Zipra1/SlimeNRF-Fuimini/Dock/Dock PCB/silkscreen.png

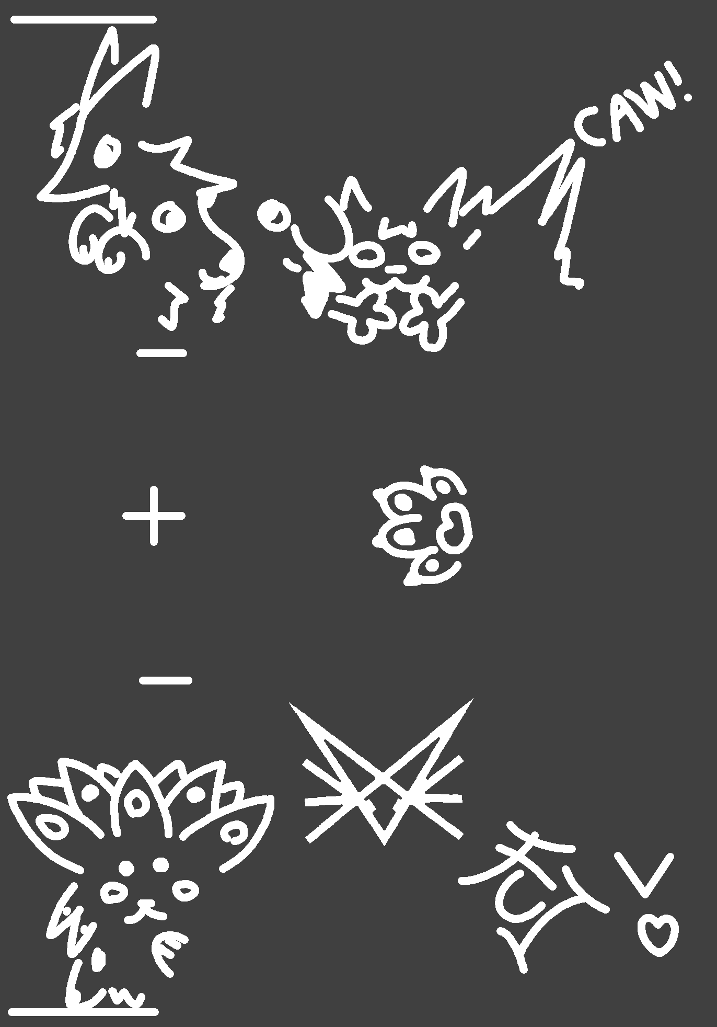
Dock/Dock PCB/silkscreen.png
