Zipra1/SlimeNRF-Fuimini/Dock/Photos/Processed/backhang.png

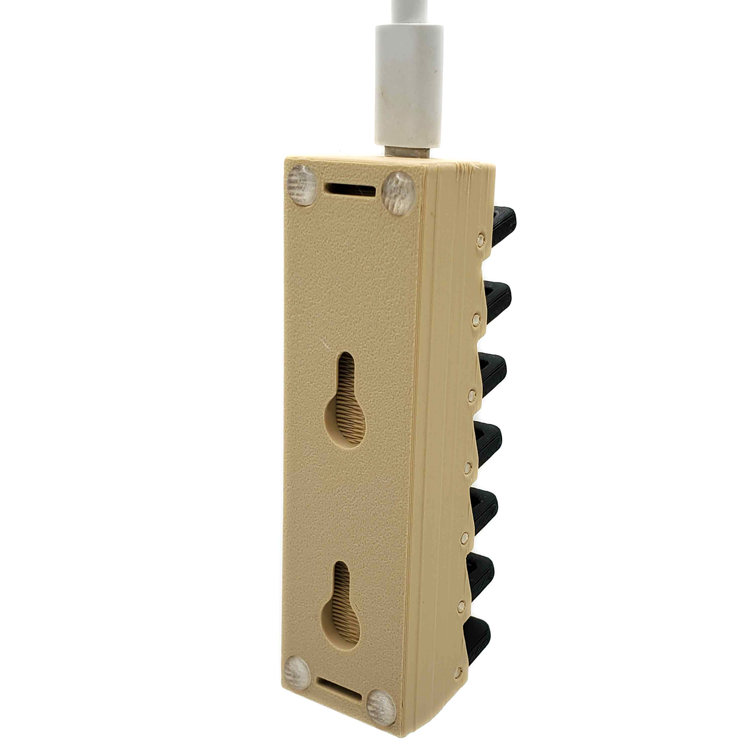
Dock/Photos/Processed/backhang.png
