Zipra1/SlimeNRF-Fuimini/Dock/Photos/Processed/fronthang.png

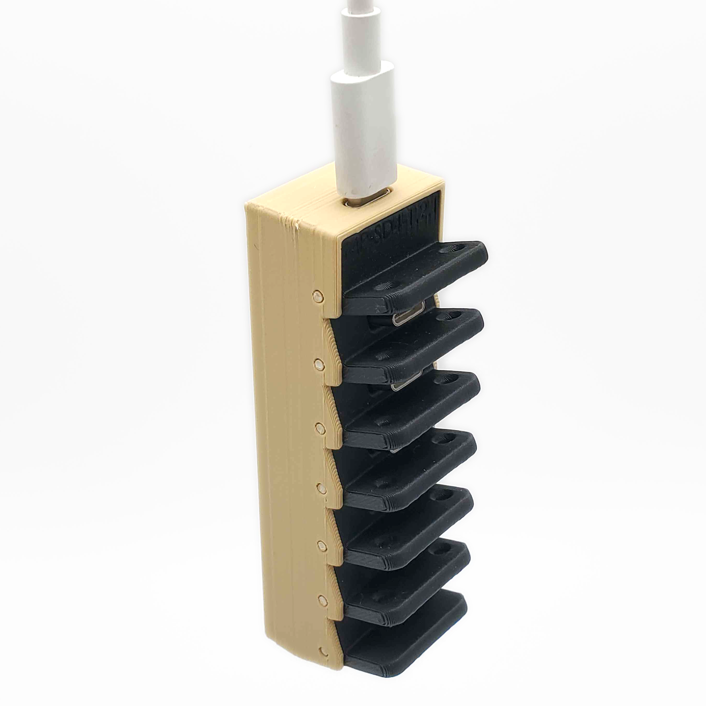
Dock/Photos/Processed/fronthang.png
