Zipra1/SlimeNRF-Fuimini/Dock/Photos/Processed/frontiso.png

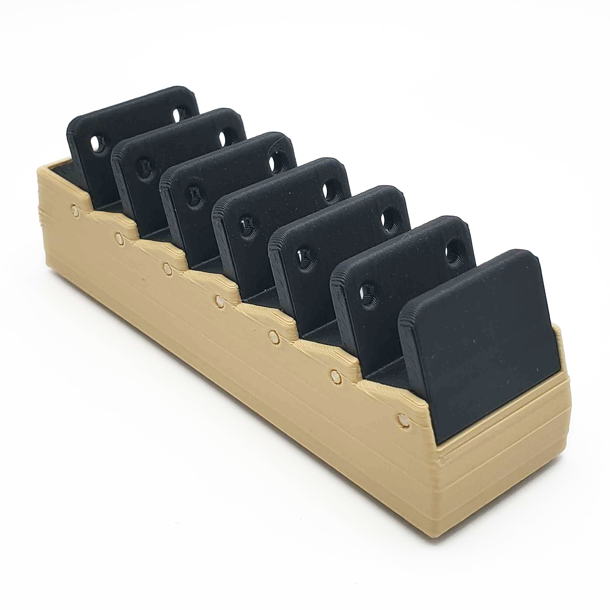
Dock/Photos/Processed/frontiso.png
