Zipra1/SlimeNRF-Fuimini/Dock/Photos/Processed/iso.png

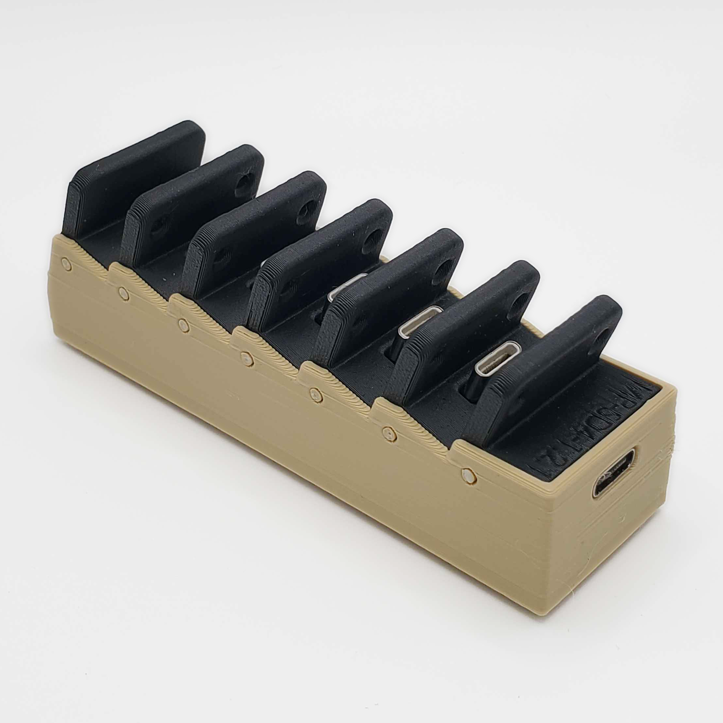
Dock/Photos/Processed/iso.png
