Zipra1/SlimeNRF-Fuimini/Dock/Photos/Raw/frontisotracker.jpg

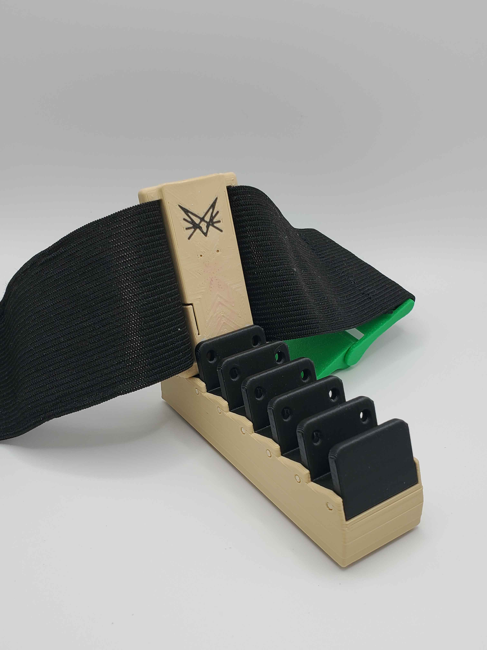
Dock/Photos/Raw/frontisotracker.jpg
