Zipra1/SlimeNRF-Fuimini/Dock/Photos/Raw/fullback.jpg

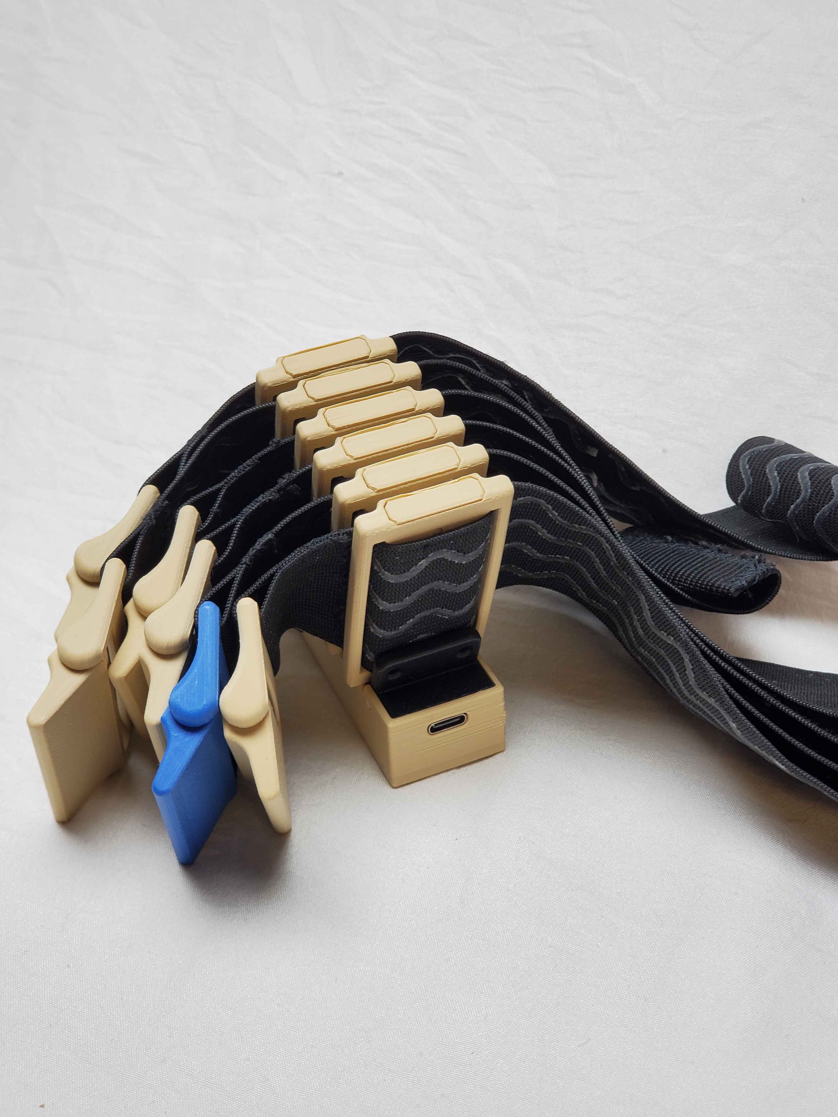
Dock/Photos/Raw/fullback.jpg
