Zipra1/SlimeNRF-Fuimini/Dock/Photos/Raw/fullfront.jpg

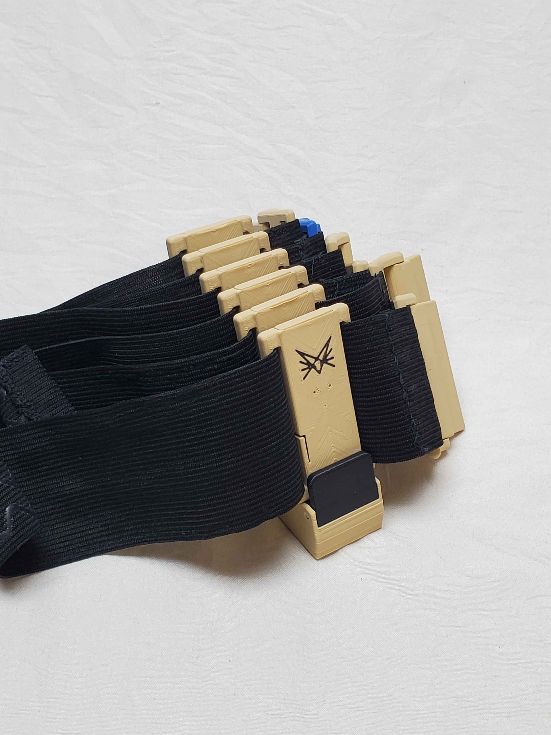
Dock/Photos/Raw/fullfront.jpg
