Zipra1/SlimeNRF-Fuimini/Dock/Photos/Raw/hangfront.jpg

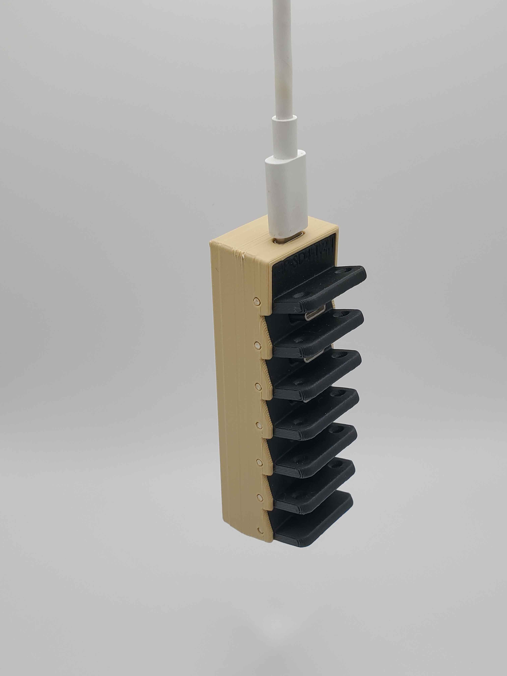
Dock/Photos/Raw/hangfront.jpg
