Zipra1/SlimeNRF-Fuimini/Receiver/Extension cable/20241215_205650.jpg

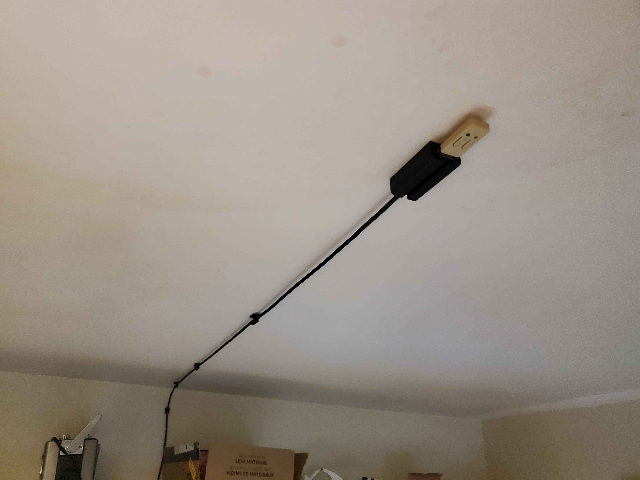
Receiver/Extension cable/20241215_205650.jpg
