Zipra1/SlimeNRF-Fuimini/Receiver/Photos/Processed/dongle1.png

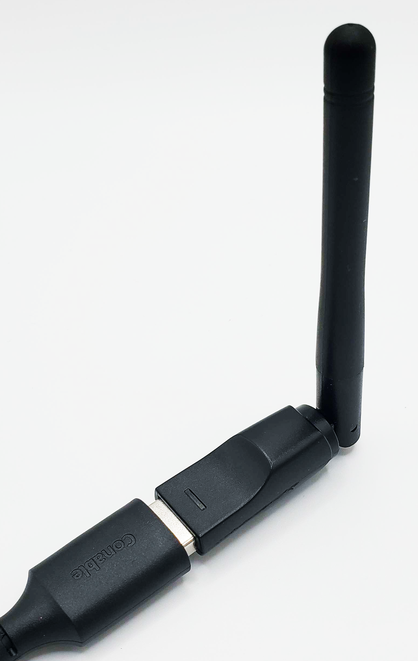
Receiver/Photos/Processed/dongle1.png
