Zipra1/SlimeNRF-Fuimini/Receiver/Photos/Processed/dongle2.png

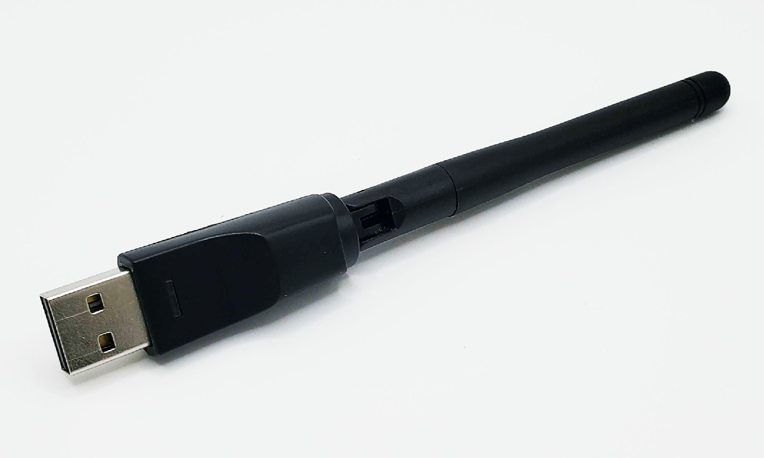
Receiver/Photos/Processed/dongle2.png
