Zipra1/SlimeNRF-Fuimini/Receiver/Photos/Processed/iso.png

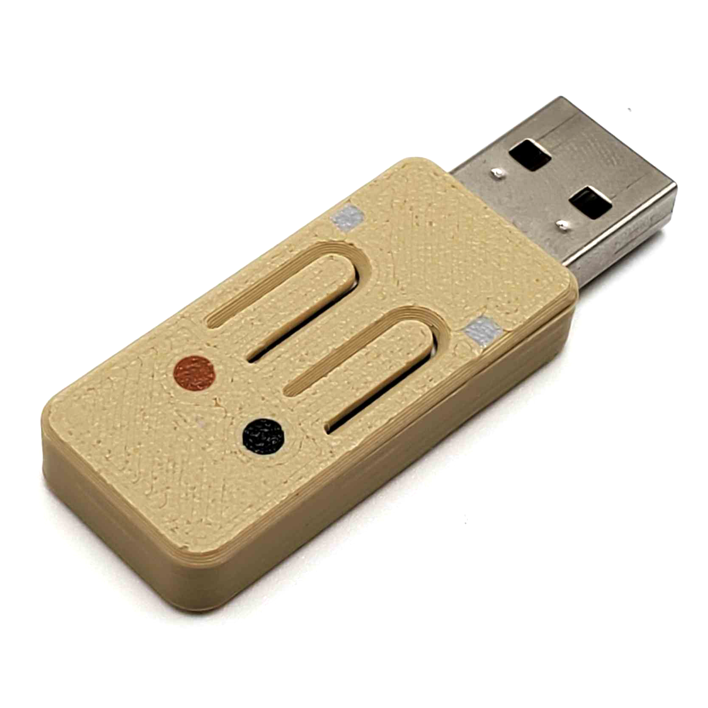
Receiver/Photos/Processed/iso.png
