Zipra1/SlimeNRF-Fuimini/Receiver/Photos/Processed/isoback.png

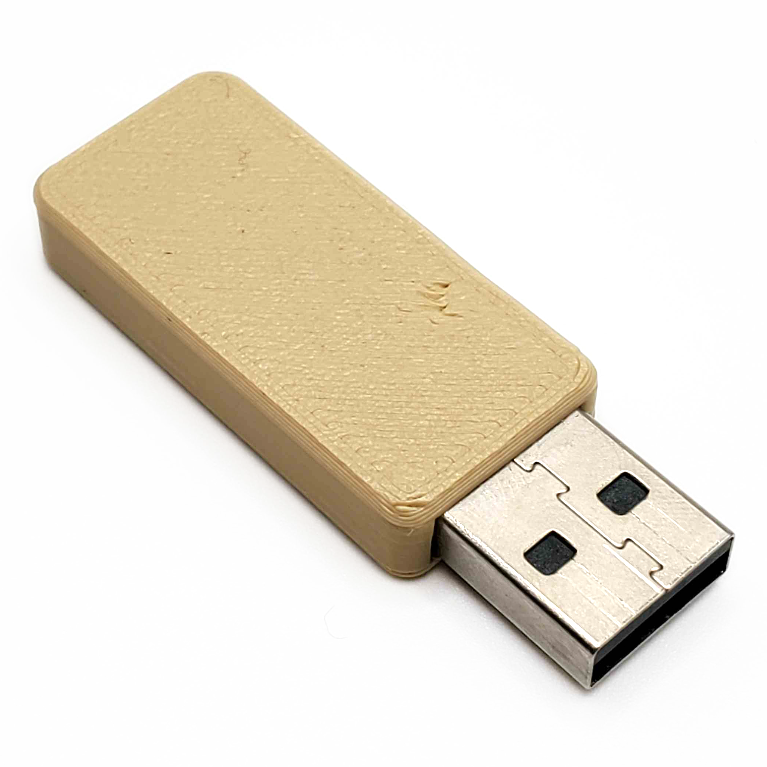
Receiver/Photos/Processed/isoback.png
