Zipra1/SlimeNRF-Fuimini/Receiver/Photos/Raw/20241223_184920.jpg

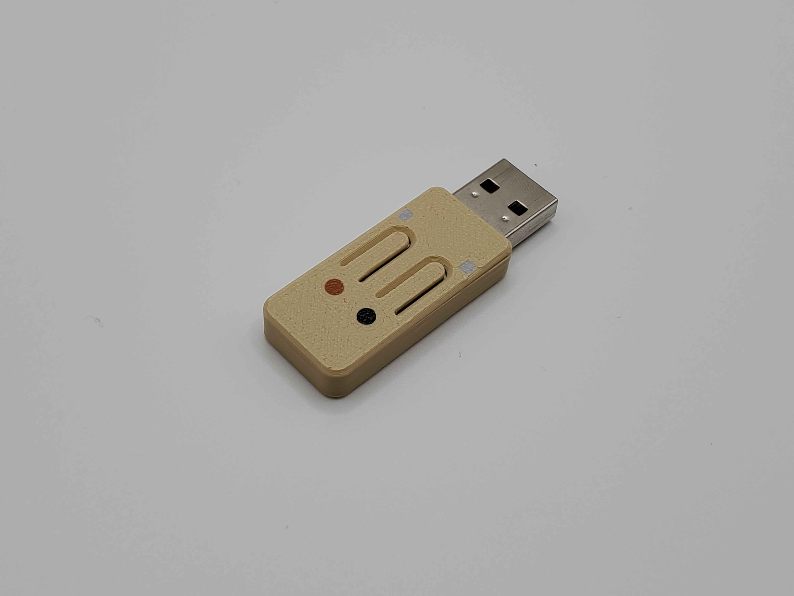
Receiver/Photos/Raw/20241223_184920.jpg
