Zipra1/SlimeNRF-Fuimini/Tracker/ICM-42688-P PCB/Cat Pad.png

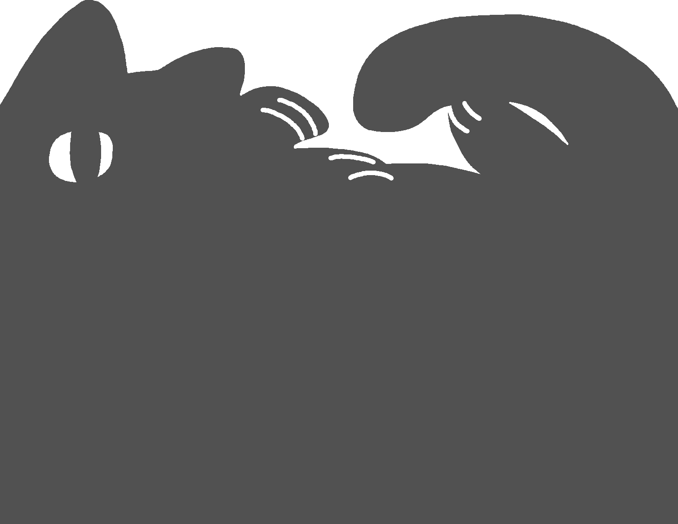
Tracker/ICM-42688-P PCB/Cat Pad.png
