Zipra1/SlimeNRF-Fuimini/Tracker/ICM-42688-P PCB/Silkscreen.png

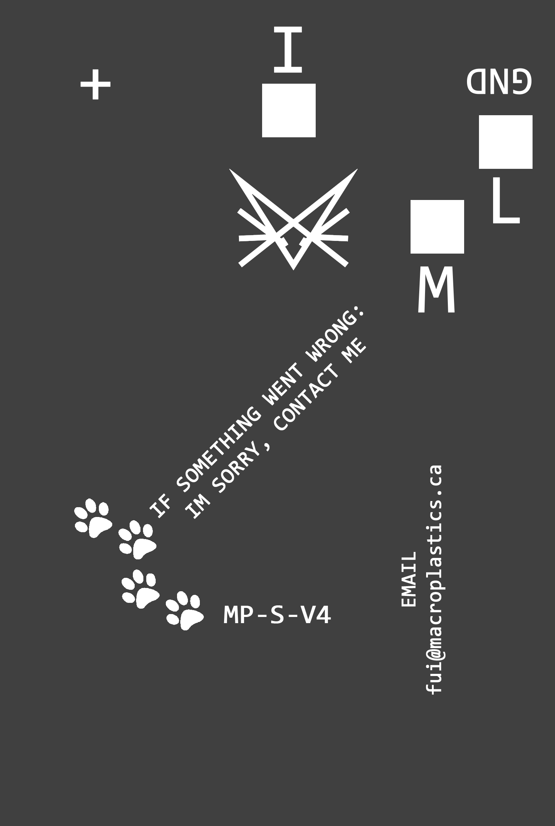
Tracker/ICM-42688-P PCB/Silkscreen.png
