Zipra1/SlimeNRF-Fuimini/Tracker/Photos/Processed/iso.png

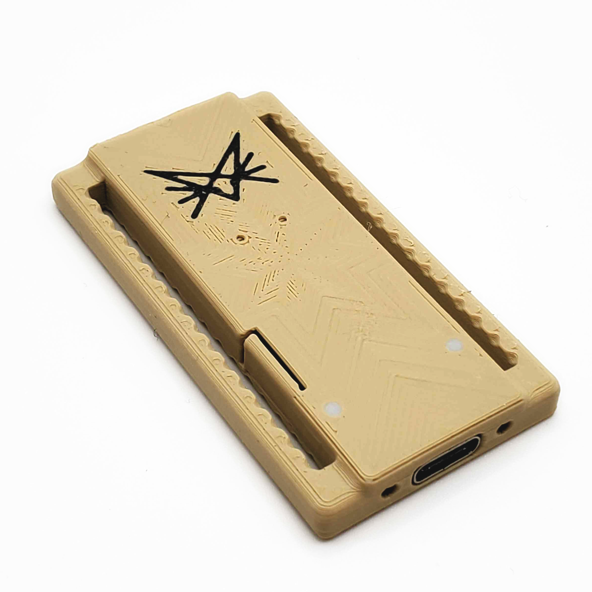
Tracker/Photos/Processed/iso.png
