Zipra1/SlimeNRF-Fuimini/Tracker/Photos/Processed/isobottom.png

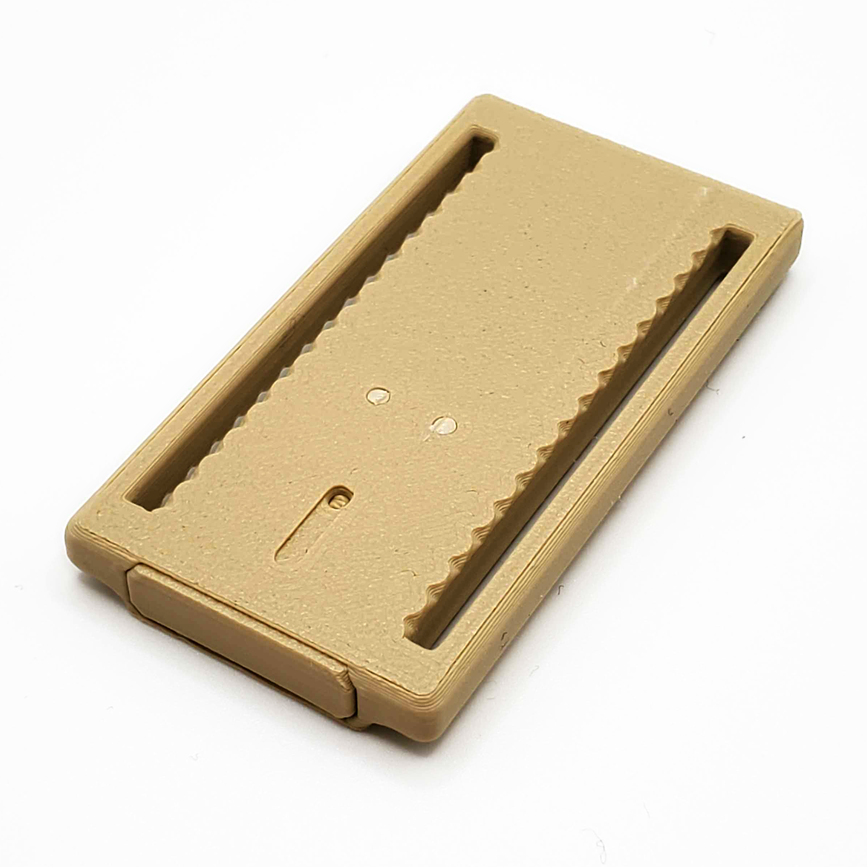
Tracker/Photos/Processed/isobottom.png
