Zipra1/SlimeNRF-Fuimini/Tracker/Photos/Processed/limb.png

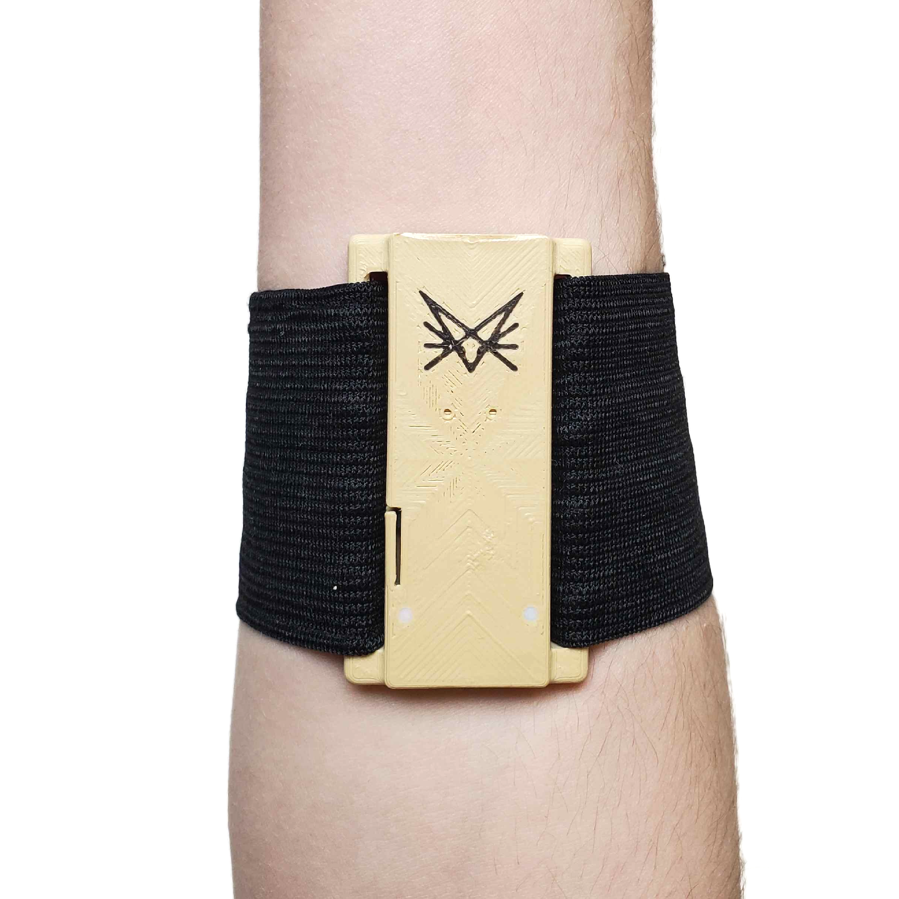
Tracker/Photos/Processed/limb.png
