Zipra1/SlimeNRF-Fuimini/Tracker/Photos/Processed/limbListing.png

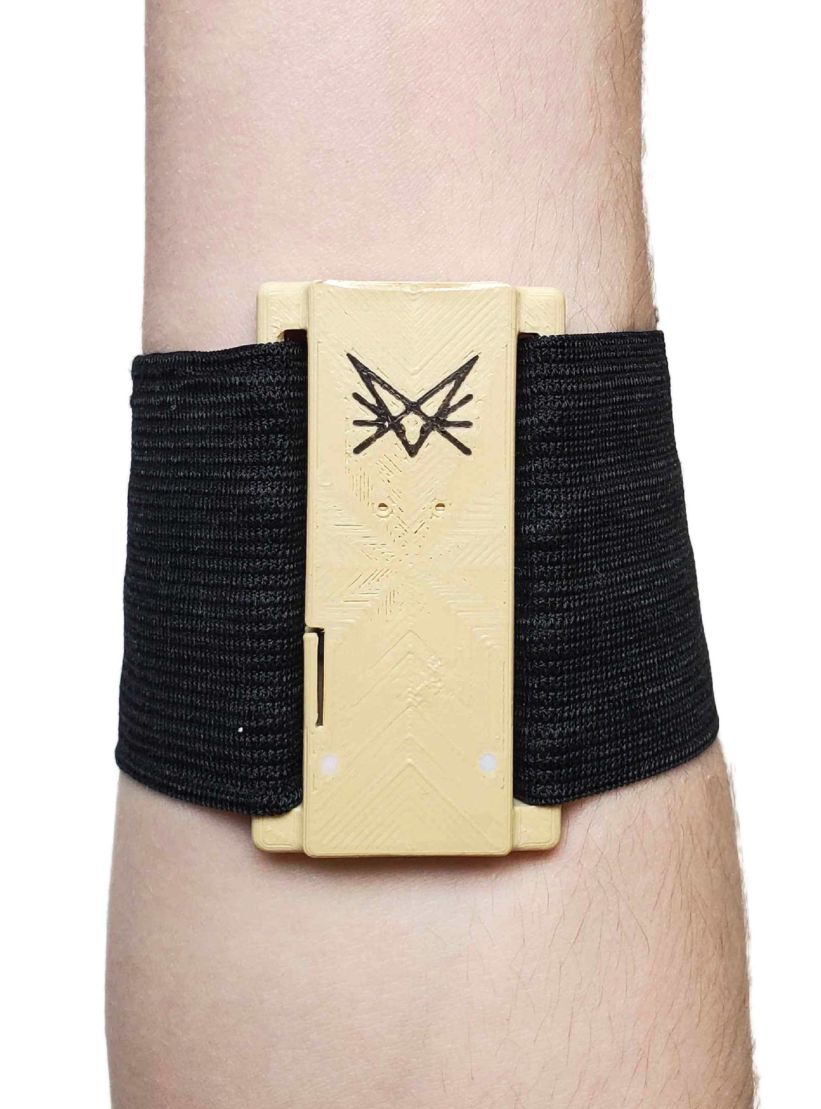
Tracker/Photos/Processed/limbListing.png
