Zipra1/SlimeNRF-Fuimini/Tracker/Photos/Processed/thickness.png

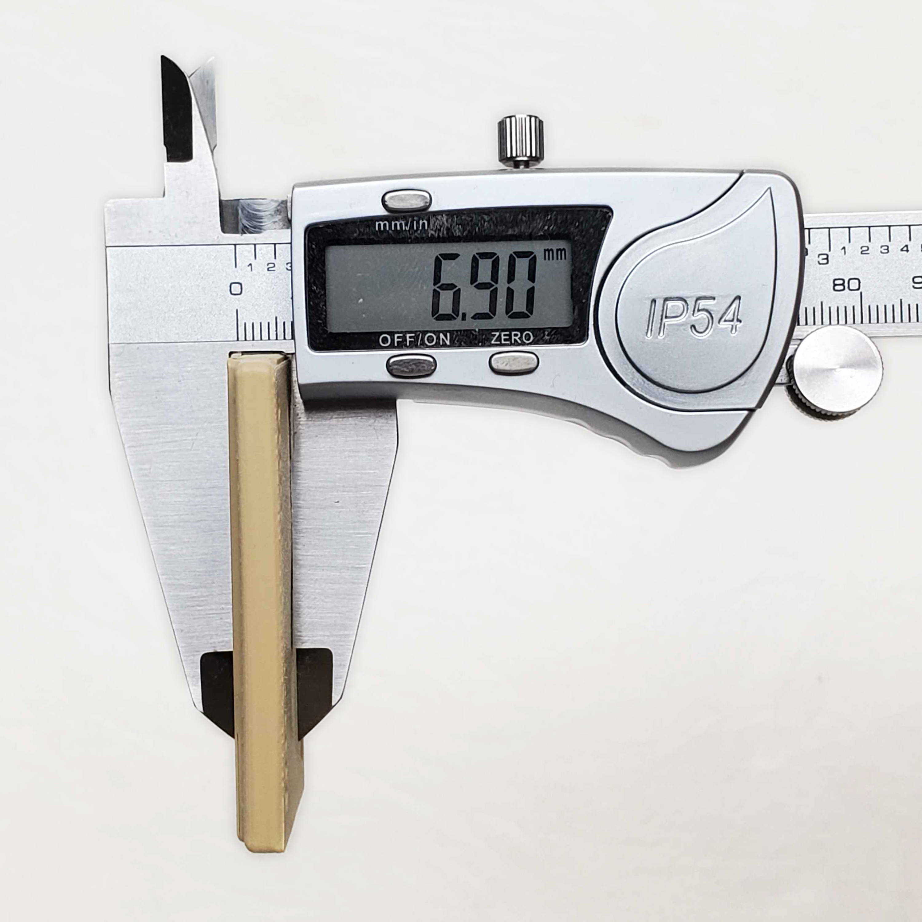
Tracker/Photos/Processed/thickness.png
