Zipra1/SlimeNRF-Fuimini/Tracker/Photos/Processed/thicknessListing.png

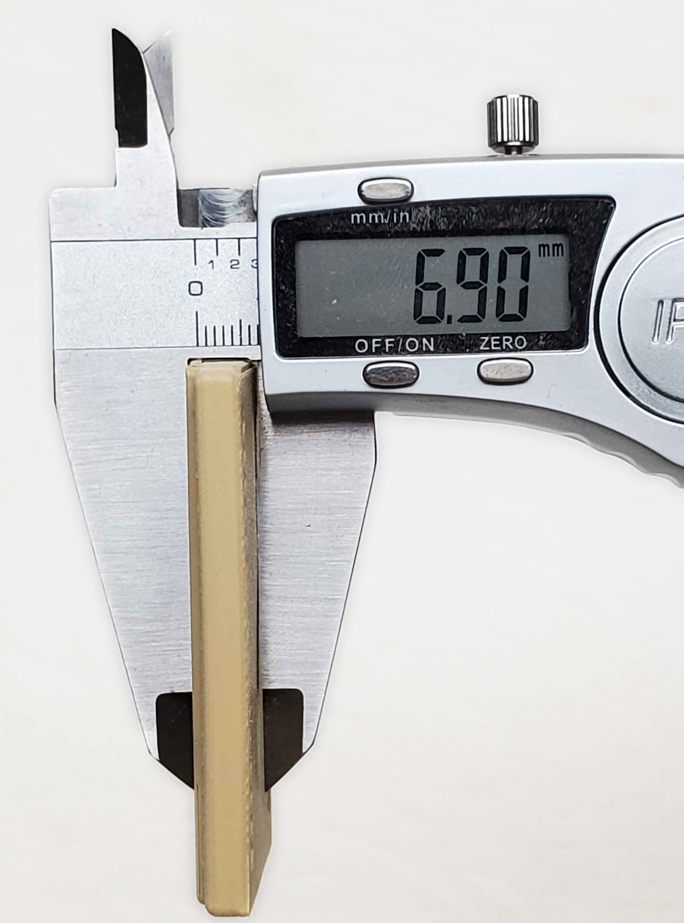
Tracker/Photos/Processed/thicknessListing.png
