Zipra1/SlimeNRF-Fuimini/Tracker/Photos/Processed/thumbnail.png

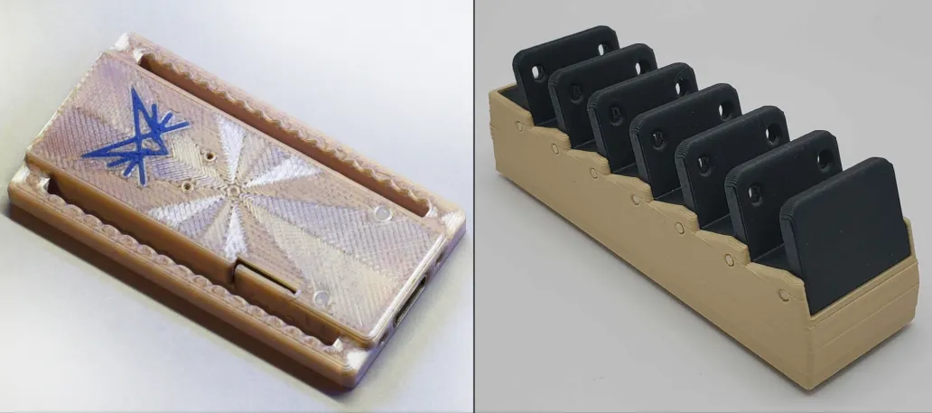
Tracker/Photos/Processed/thumbnail.png
