Zipra1/SlimeNRF-Fuimini/Tracker/Photos/Raw/handful.jpg

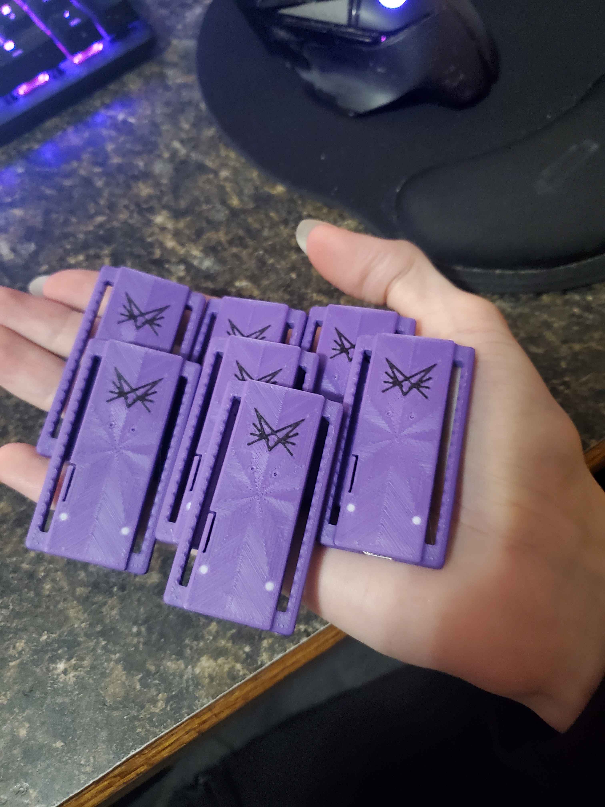
Tracker/Photos/Raw/handful.jpg
