Zipra1/SlimeNRF-Fuimini/Tracker/Photos/Raw/isobottom.jpg

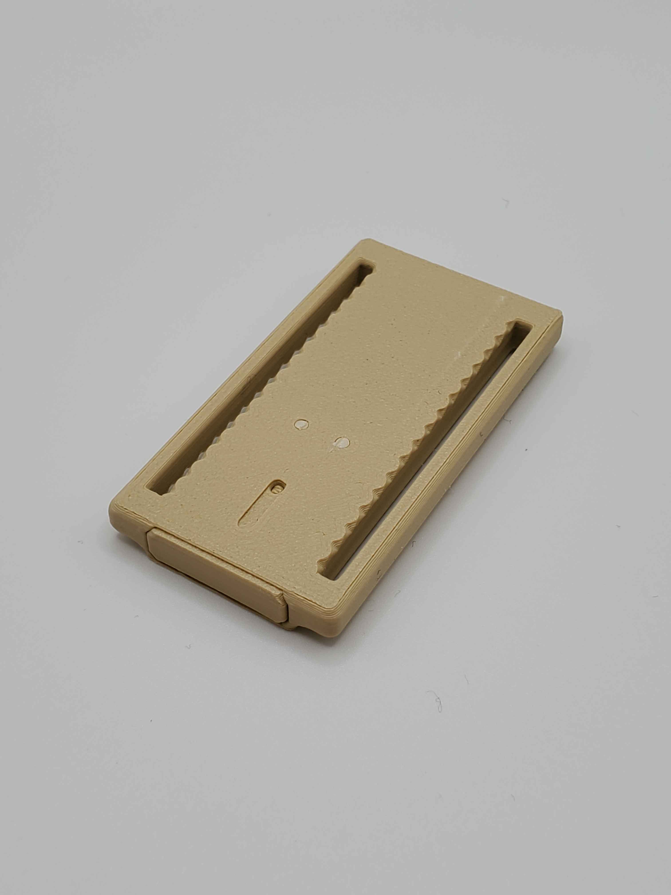
Tracker/Photos/Raw/isobottom.jpg
