Zipra1/SlimeNRF-Fuimini/Tracker/Photos/Raw/isostrap.jpg

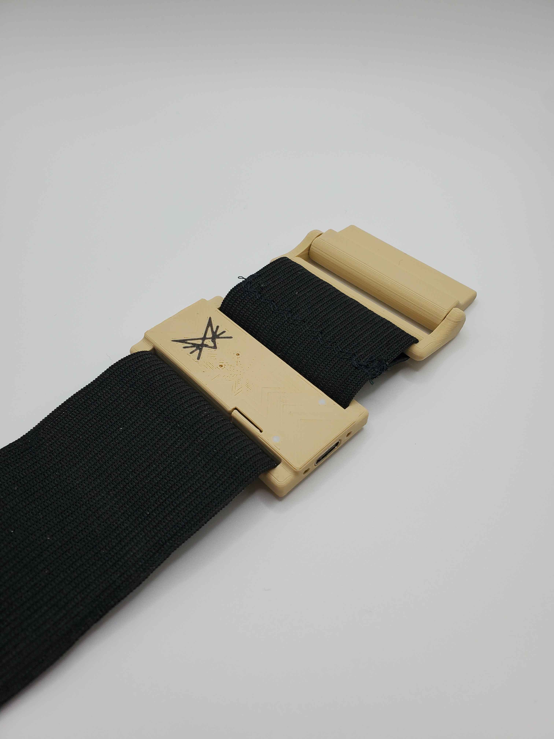
Tracker/Photos/Raw/isostrap.jpg
