Zipra1/SlimeNRF-Fuimini/Receiver/Extension cable/Ceiling mount.STEP

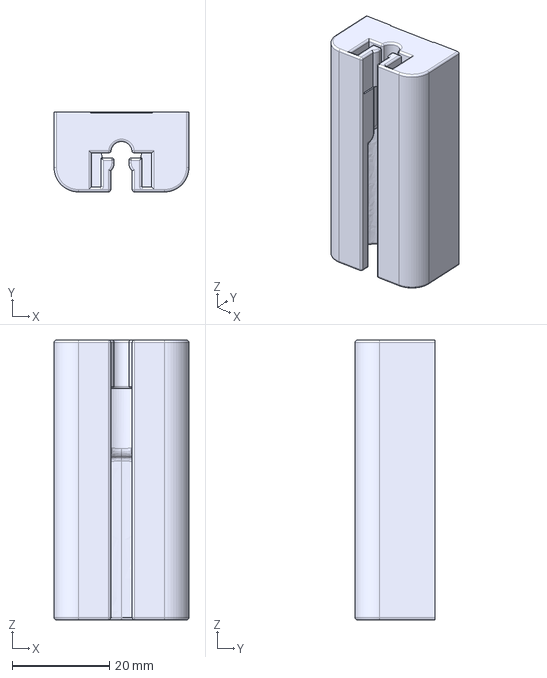
[picture p59: CAD file, 2024-12-14]
Receiver/Extension cable/Ceiling mount.STEP
27.7 x 16.4 x 57.5 mm
