Zipra1/SlimeNRF-Fuimini/Straps/Cam Lock Shoulder Strap.STEP

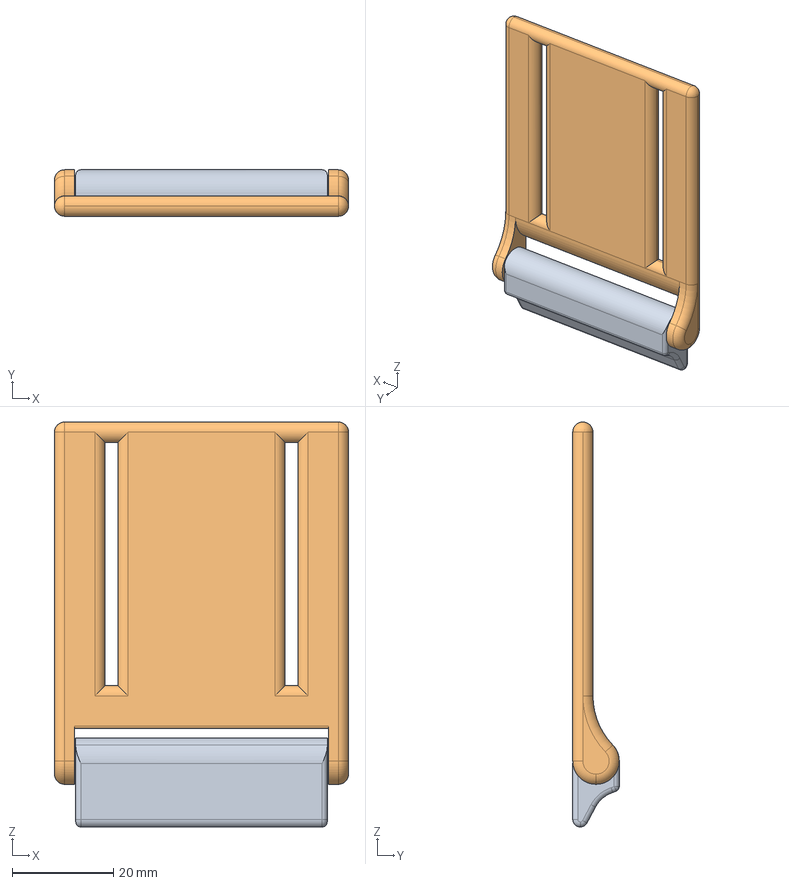
[picture p60: CAD file, 2025-08-03]
Straps/Cam Lock Shoulder Strap.STEP
58.0 x 9.18 x 79.9 mm
