Zipra1/SlimeNRF-Fuimini/Tracker/3D Models/Case.3mf

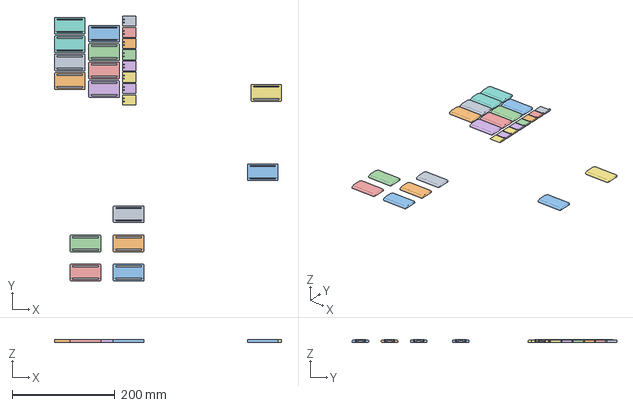
[picture p61: CAD file, 2025-05-23]
Tracker/3D Models/Case.3mf
442.4 x 516.1 x 6.48 mm
End Cap.STL x 8
End Cap x 15
