Zipra1/SlimeNRF-Fuimini/Dock/3D Models/SV4 dock (10).STEP

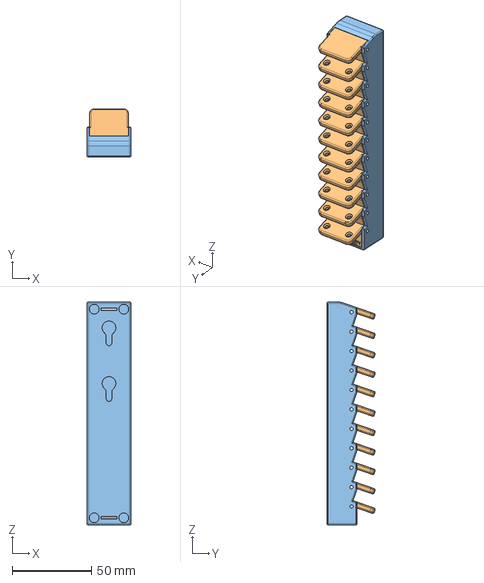
[picture p62: CAD file, 2024-12-31]
Dock/3D Models/SV4 dock (10).STEP
27.7 x 30.5 x 140.5 mm
