Zipra1/SlimeNRF-Fuimini/Straps/Chesty Mount.STEP

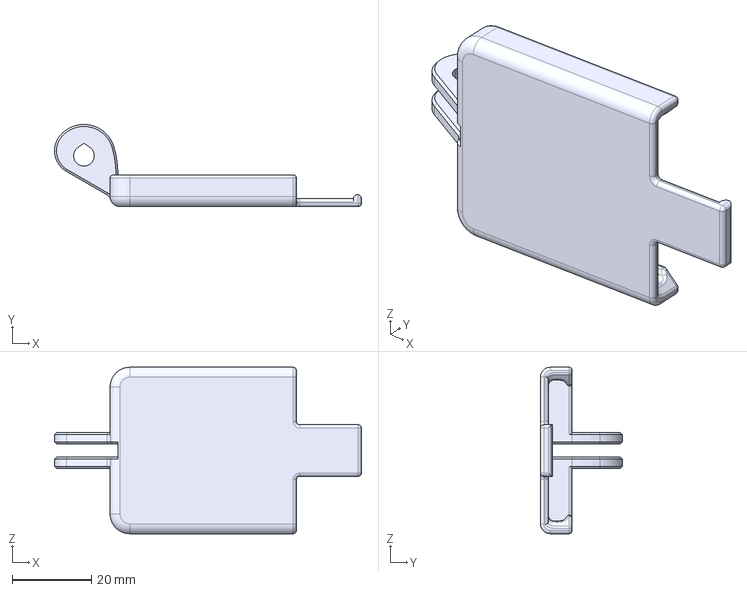
[picture p63: CAD file, 2025-08-03]
Straps/Chesty Mount.STEP
77.4 x 20.7 x 42.0 mm
