Zipra1/SlimeNRF-Fuimini/Straps/Velcro strap quick release.STEP

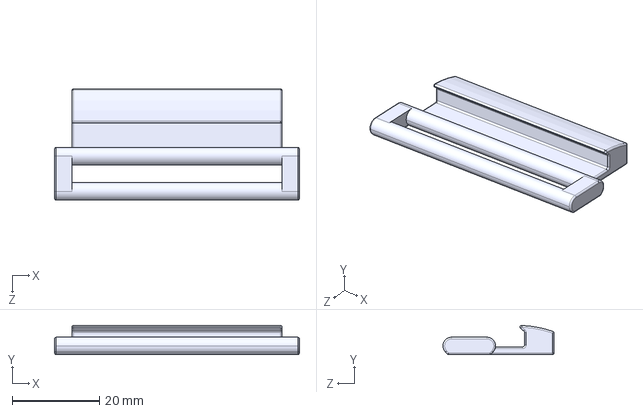
[picture p64: CAD file, 2025-08-03]
Straps/Velcro strap quick release.STEP
56.3 x 6.70 x 25.5 mm
