Zipra1/SlimeNRF-Fuimini/Dock/3D Models/SV4 dock.STEP

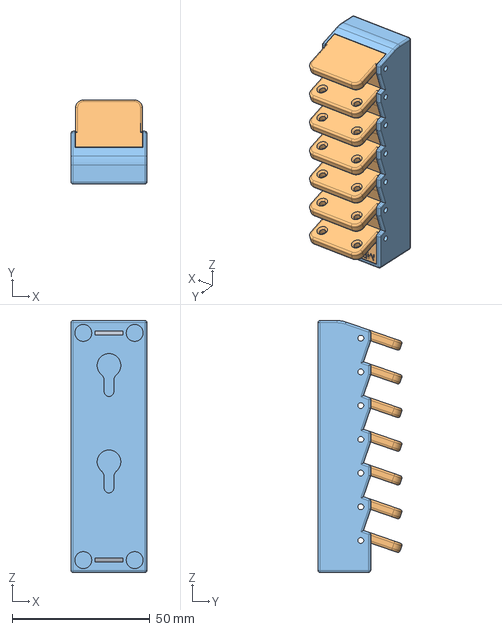
[picture p65: CAD file, 2024-12-11]
Dock/3D Models/SV4 dock.STEP
27.7 x 30.5 x 91.5 mm
