Zipra1/SlimeNRF-Fuimini/Straps/Cam Lock Shoulder Strap Back Triangle.STEP

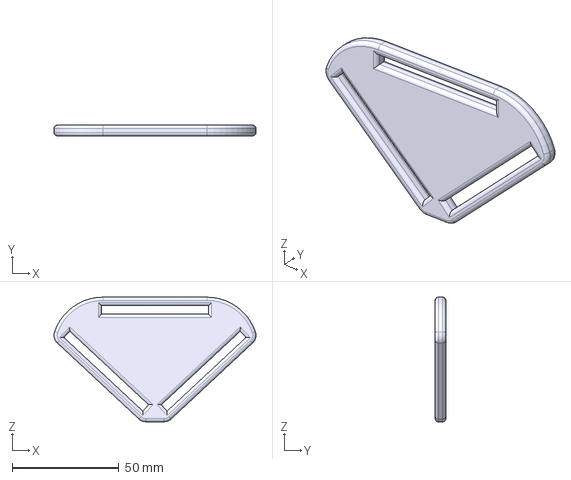
[picture p66: CAD file, 2025-05-25]
Straps/Cam Lock Shoulder Strap Back Triangle.STEP
94.7 x 5.00 x 58.4 mm
