Zipra1/SlimeNRF-Fuimini/Tracker/3D Models/End Cap.STL

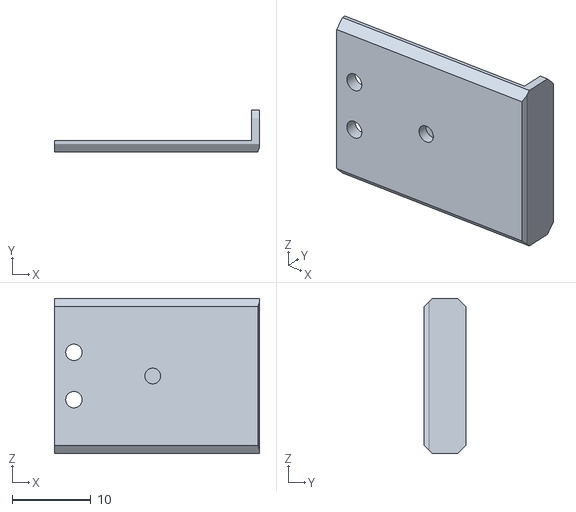
[picture p67: CAD file, 2024-12-27]
Tracker/3D Models/End Cap.STL
26.0 x 5.32 x 19.7
