Zipra1/SlimeNRF-Fuimini/Tracker/3D Models/Light Diffuser.STL

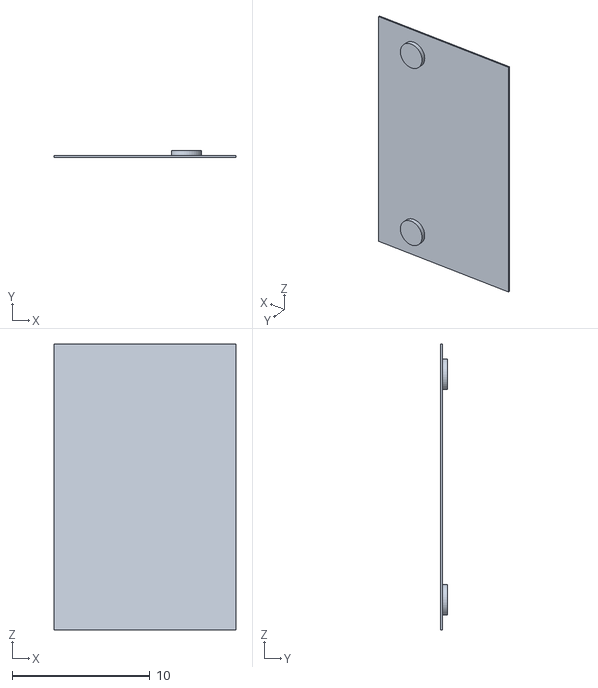
[picture p68: CAD file, 2024-12-27]
Tracker/3D Models/Light Diffuser.STL
13.2 x 0.48 x 20.8
