Zipra1/SlimeNRF-Fuimini/Tracker/3D Models/Calibration Jig.STEP

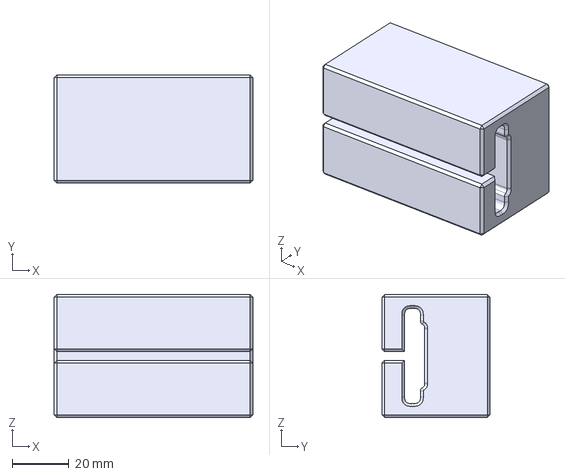
[picture p69: CAD file, 2024-12-17]
Tracker/3D Models/Calibration Jig.STEP
70.0 x 38.1 x 43.4 mm
