Zipra1/SlimeNRF-Fuimini/Tracker/3D Models/Debug Jig.STL

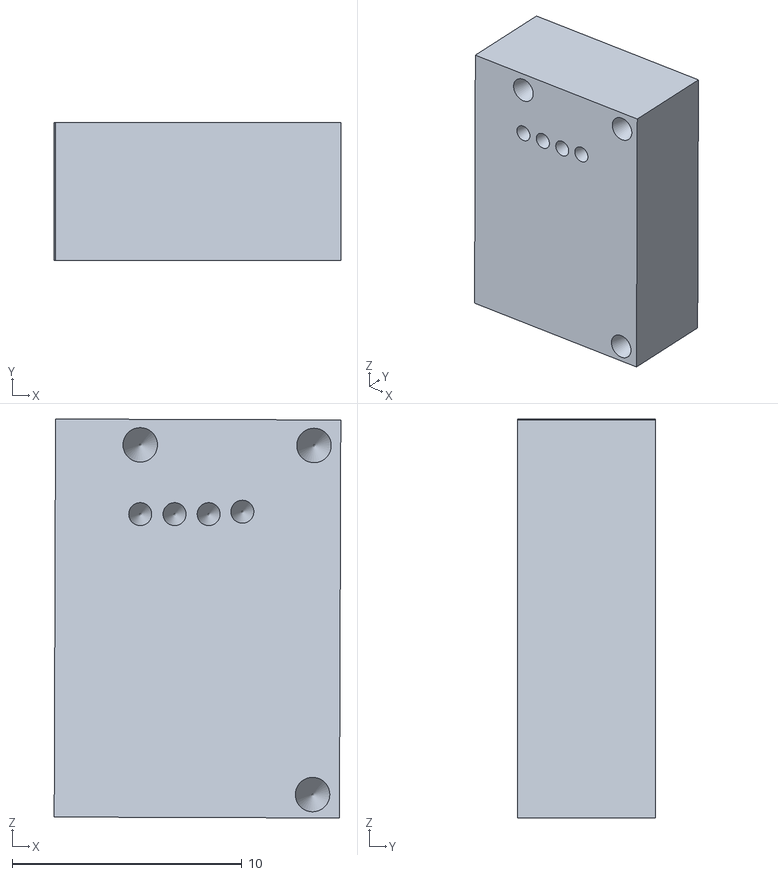
[picture p70: CAD file, 2024-11-17]
Tracker/3D Models/Debug Jig.STL
12.5 x 6.00 x 17.4
