Zipra1/SlimeNRF-Fuimini/Tracker/3D Models/Pin cutting jig.STL

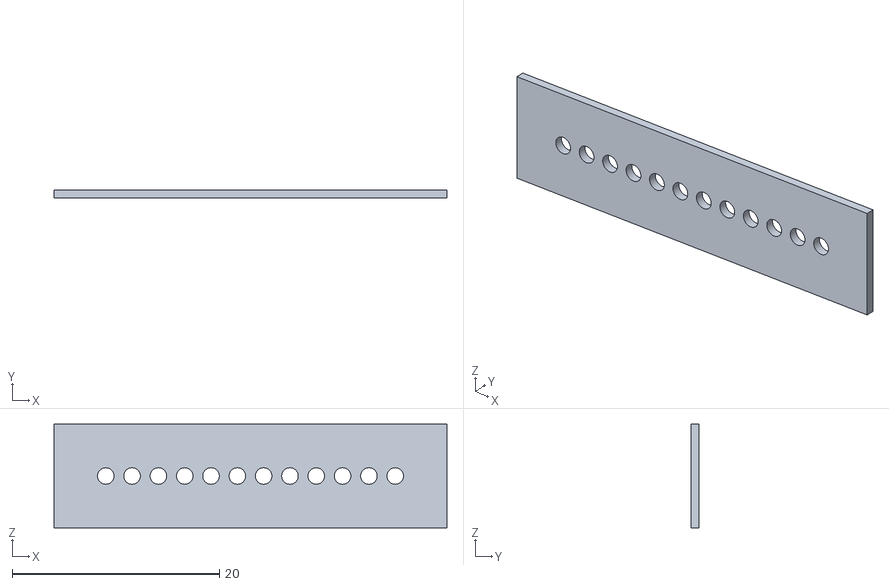
[picture p71: CAD file, 2024-11-14]
Tracker/3D Models/Pin cutting jig.STL
37.9 x 0.8 x 10.0
