Zipra1/SlimeNRF-Fuimini/Tracker/3D Models/USB_type_C_smd_24p.stp

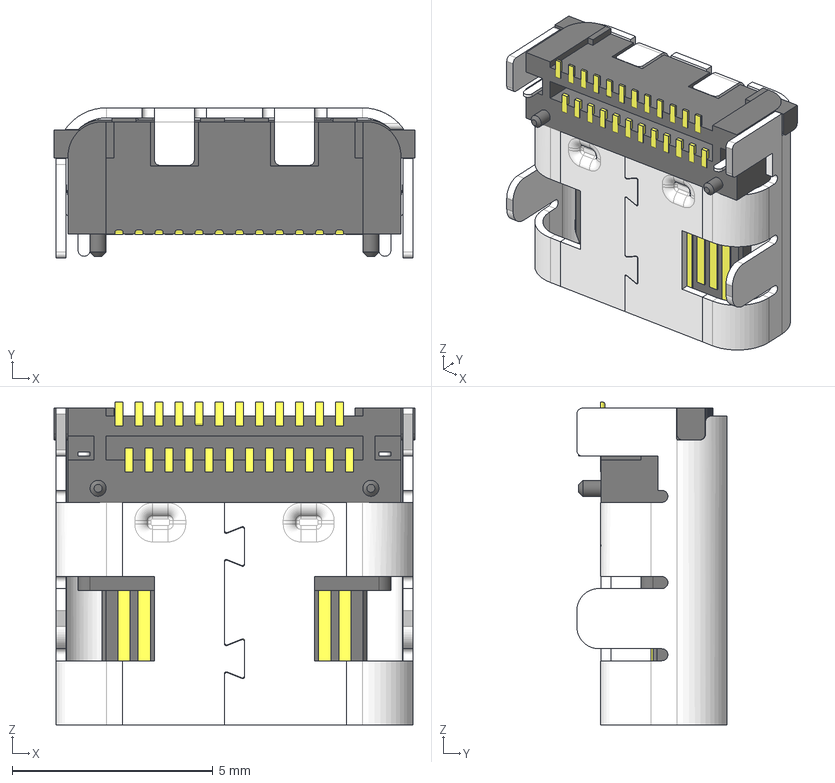
[picture p72: CAD file, 2024-11-04]
Tracker/3D Models/USB_type_C_smd_24p.stp
9.00 x 3.75 x 8.05 mm
