Zipra1/SlimeNRF-Fuimini/User manual/Individual pages/A.png

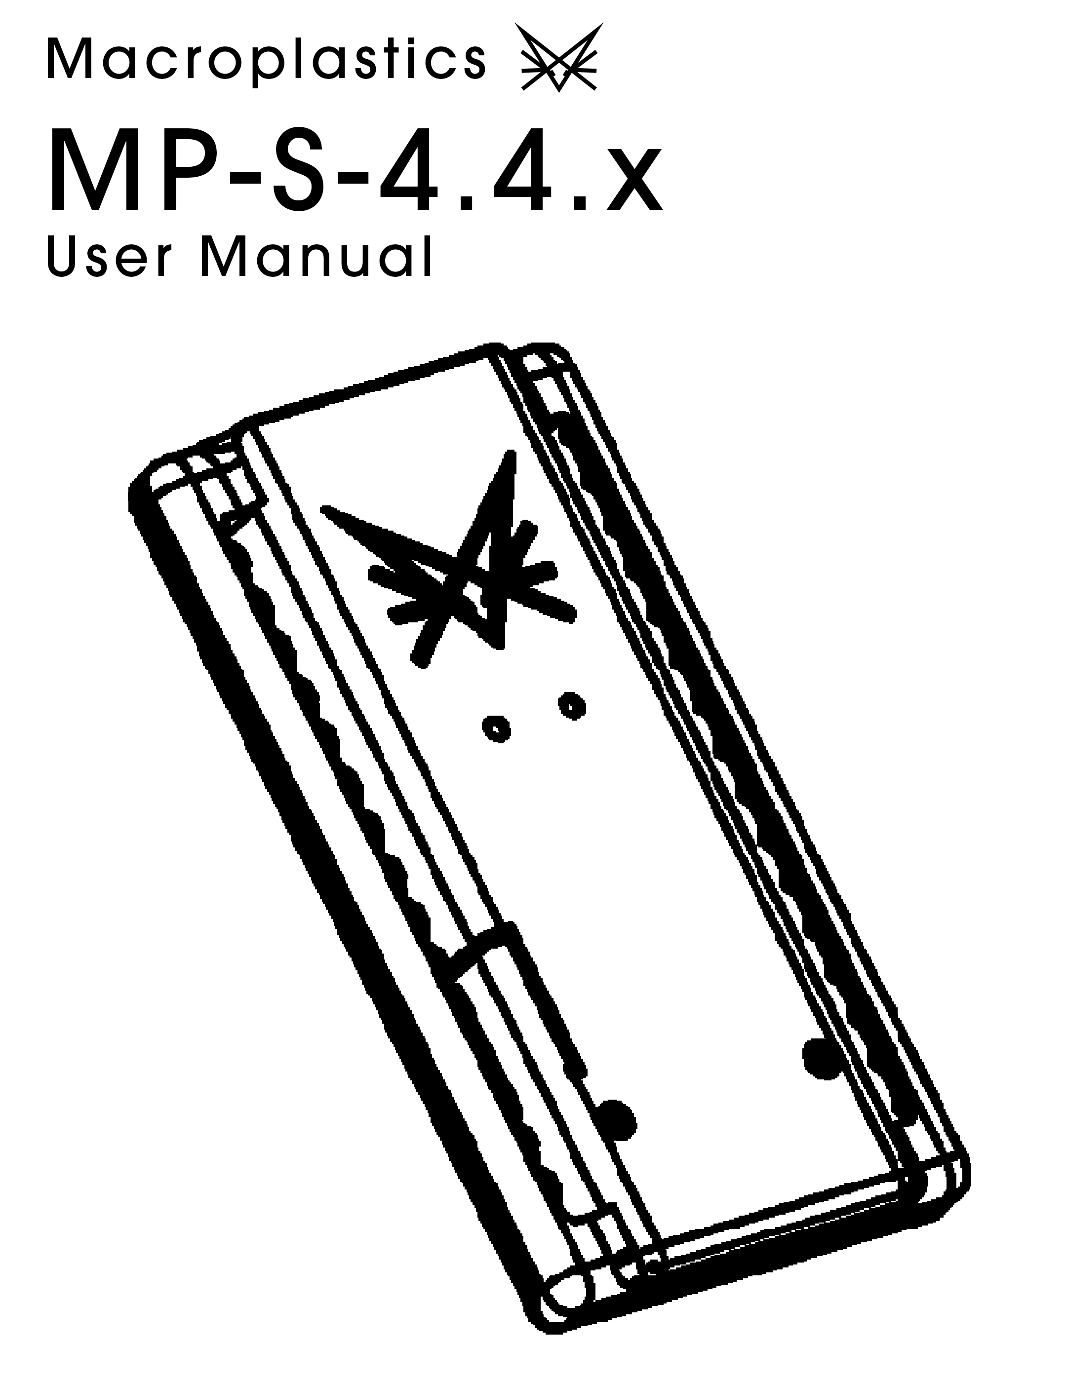
User manual/Individual pages/A.png
