Zipra1/SlimeNRF-Fuimini/User manual/Individual pages/B.png

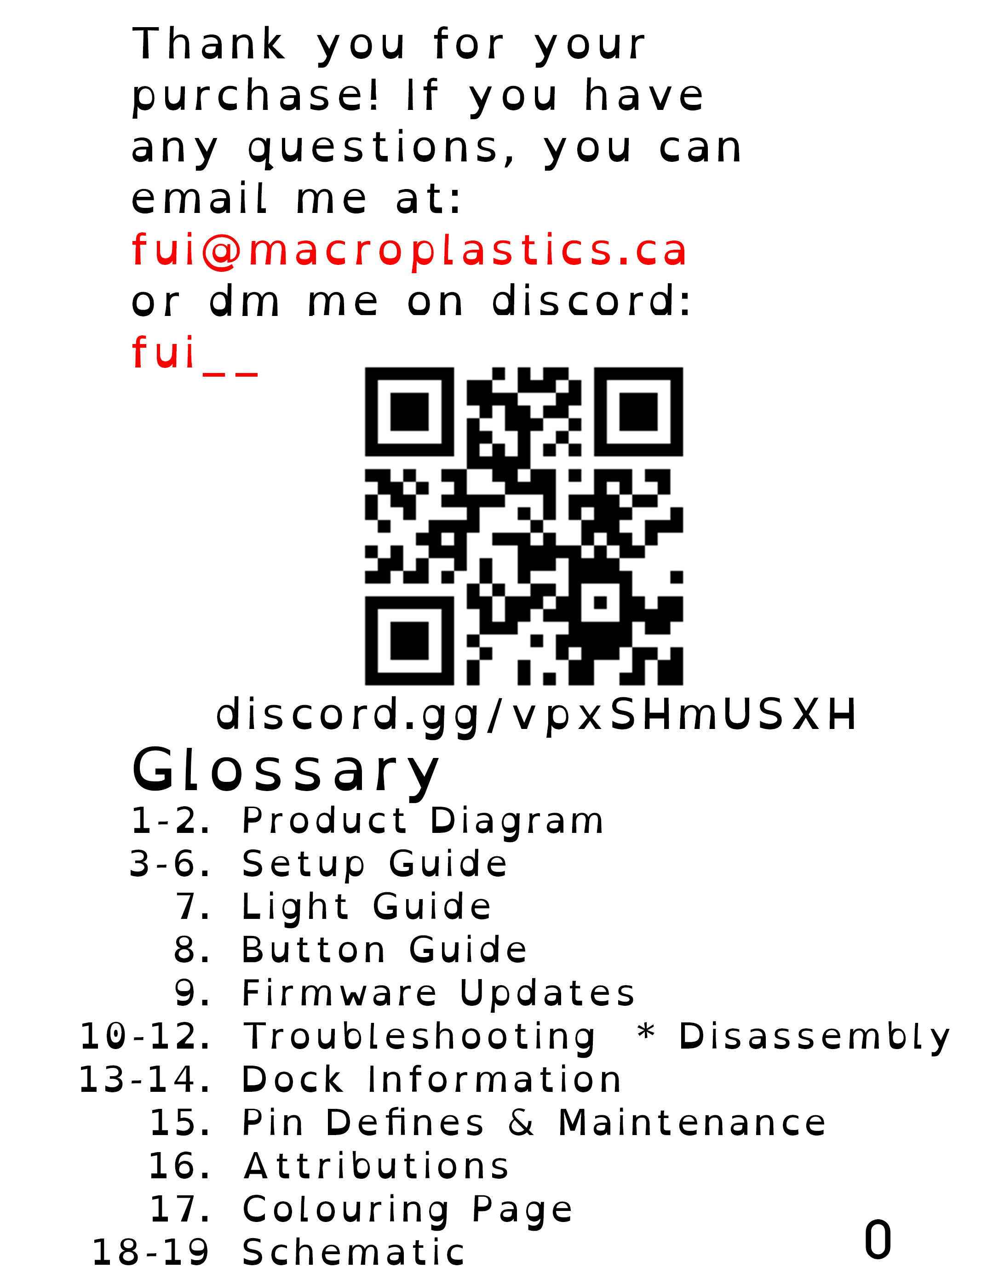
User manual/Individual pages/B.png
