Zipra1/SlimeNRF-Fuimini/User manual/Individual pages/E.png

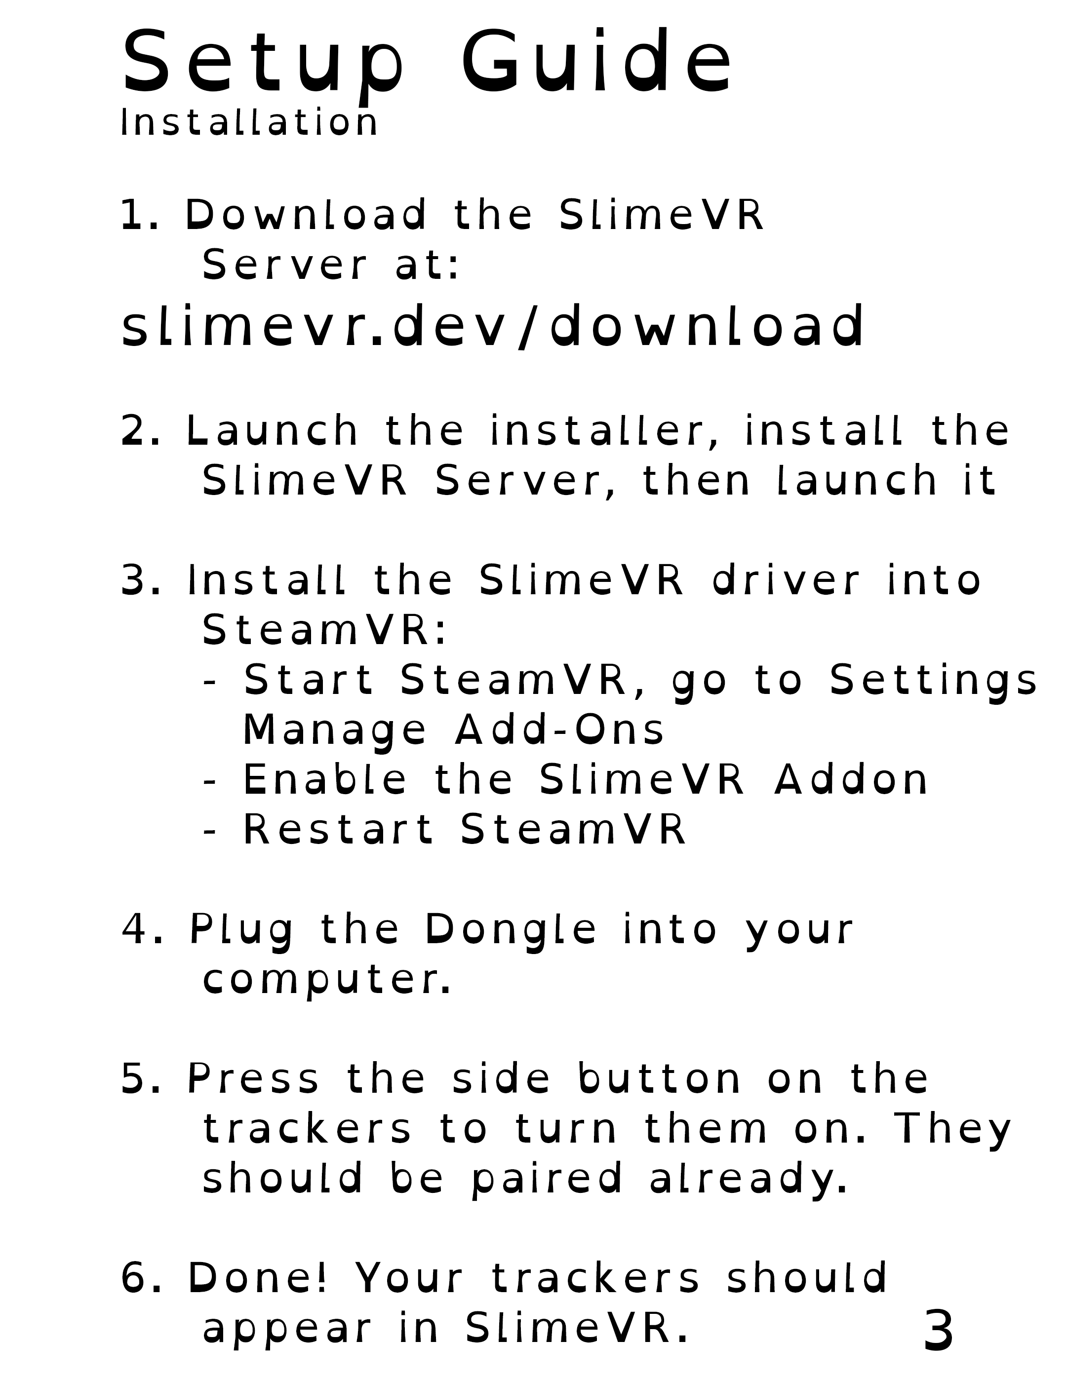
User manual/Individual pages/E.png
