Zipra1/SlimeNRF-Fuimini/User manual/Individual pages/F.png

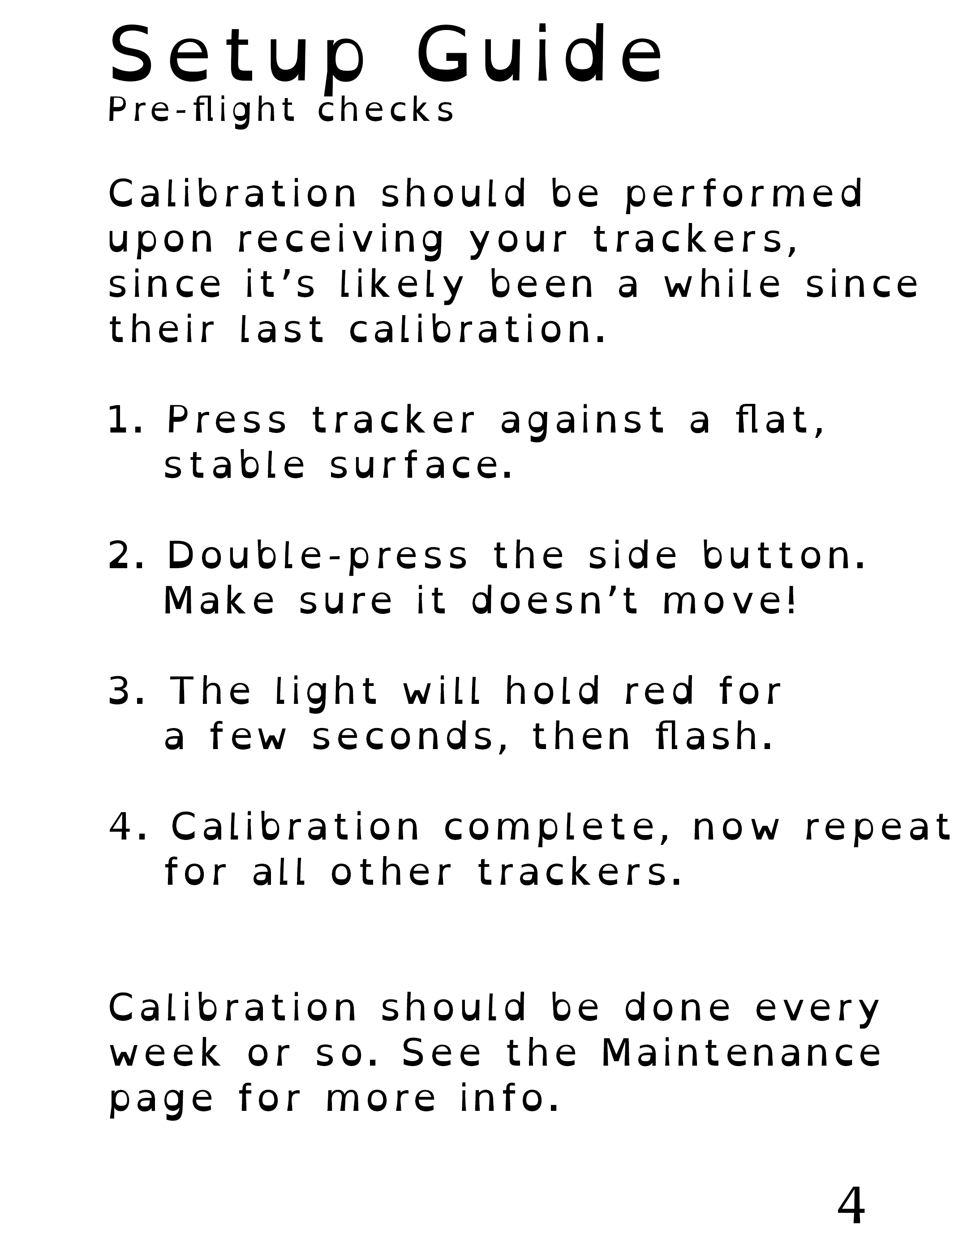
User manual/Individual pages/F.png
