Zipra1/SlimeNRF-Fuimini/User manual/Individual pages/G.png

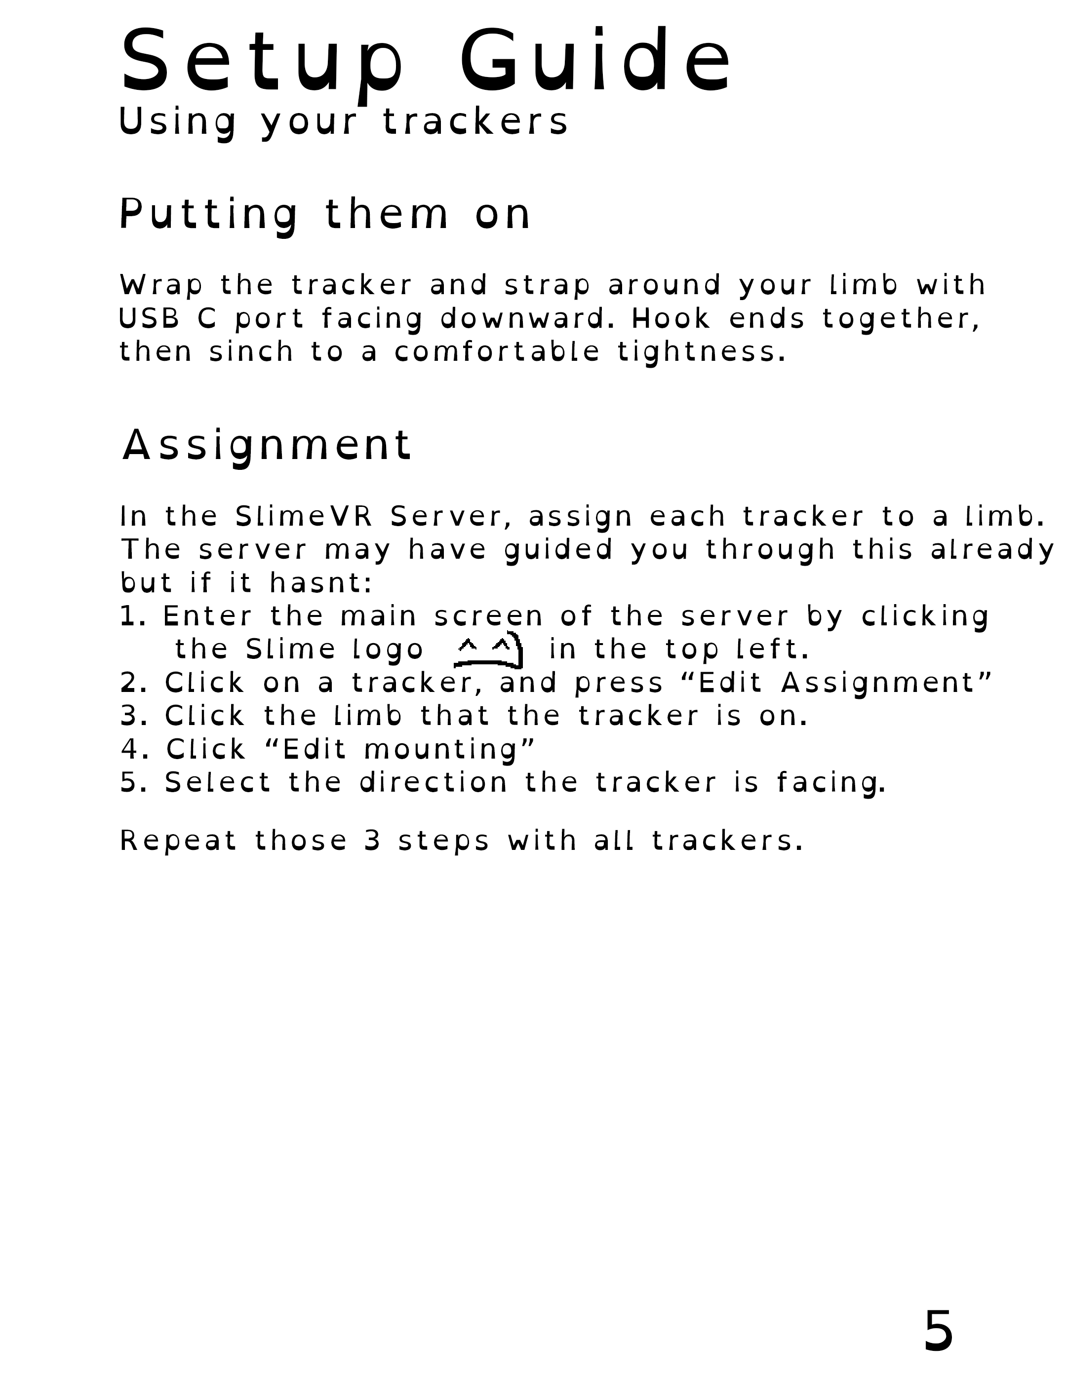
User manual/Individual pages/G.png
