Zipra1/SlimeNRF-Fuimini/User manual/Individual pages/H.png

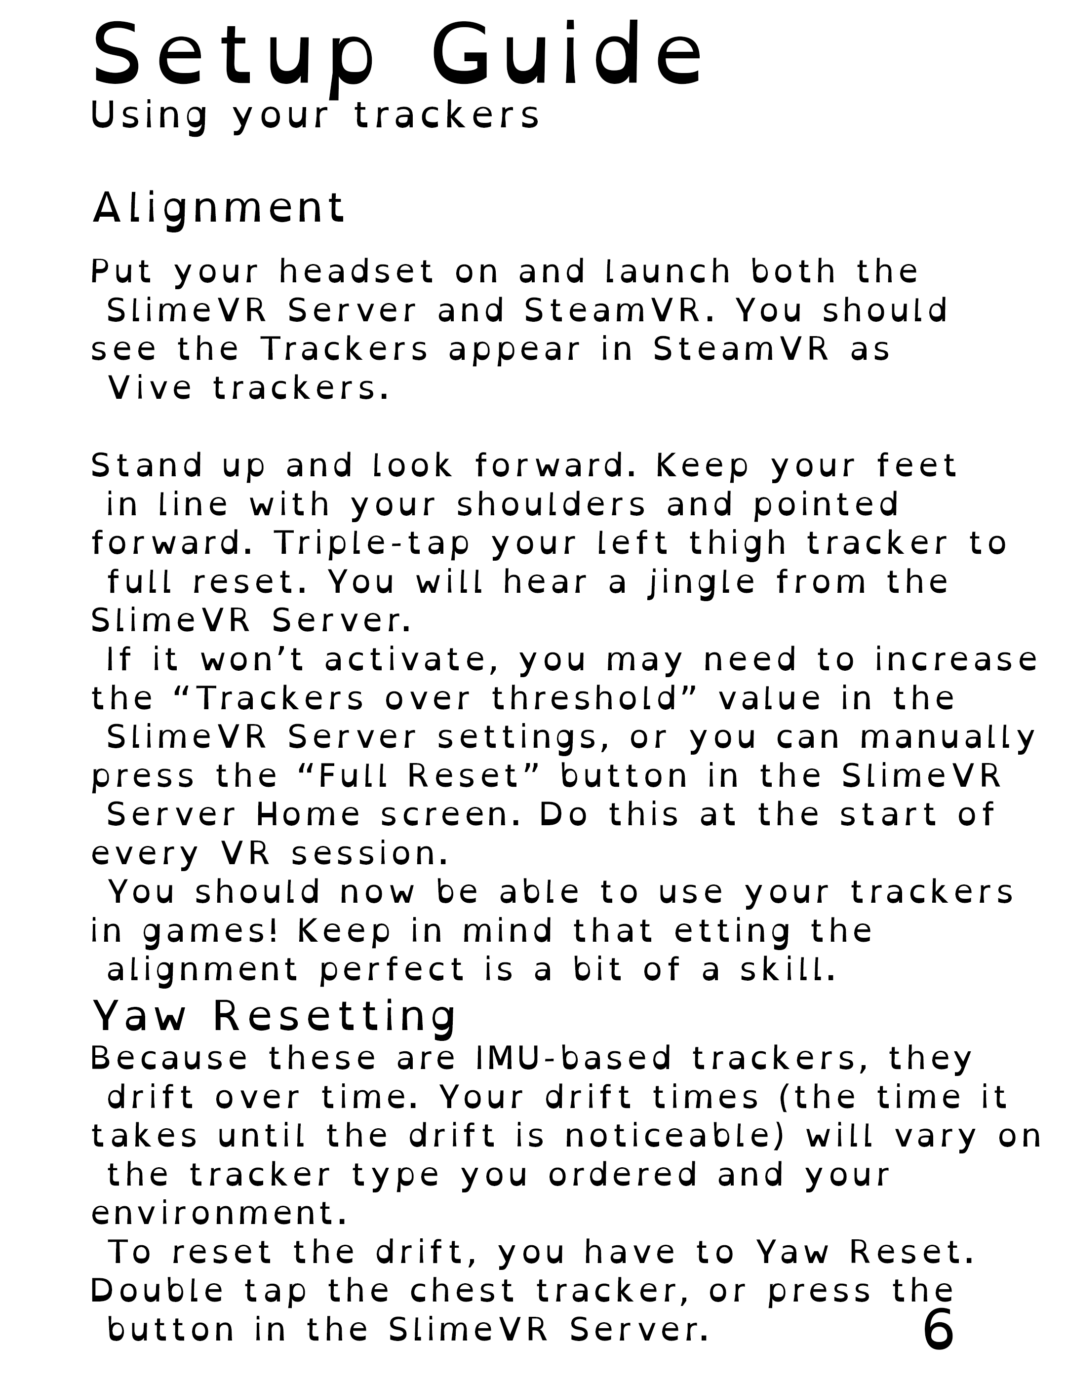
User manual/Individual pages/H.png
