Zipra1/SlimeNRF-Fuimini/User manual/Individual pages/K.png

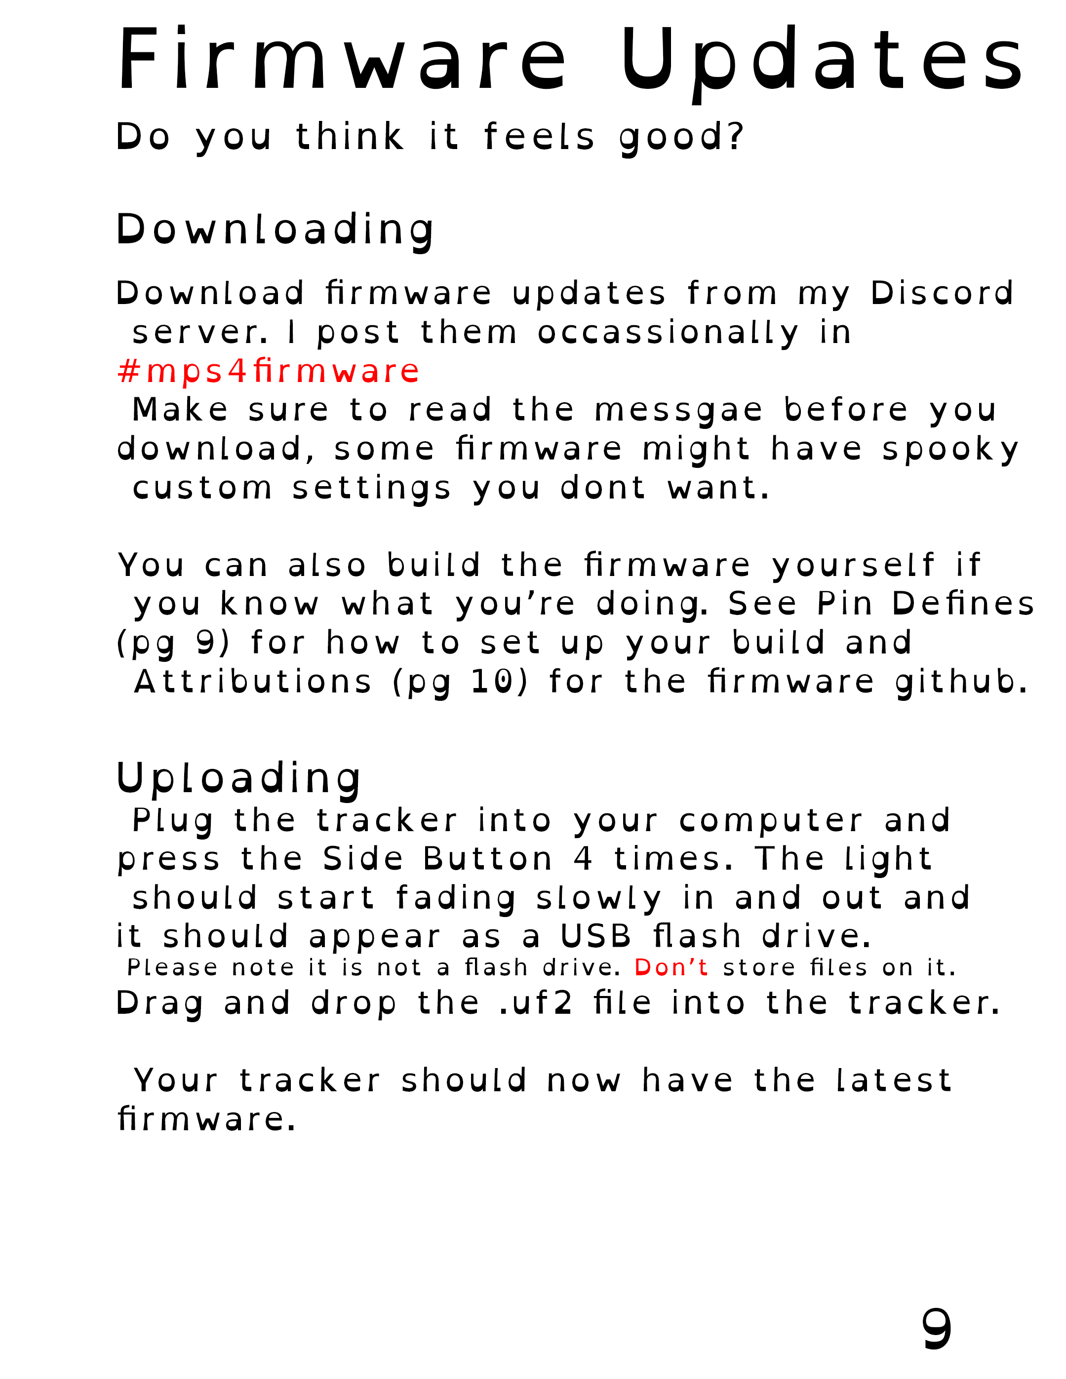
User manual/Individual pages/K.png
