Zipra1/SlimeNRF-Fuimini/User manual/Individual pages/M.png

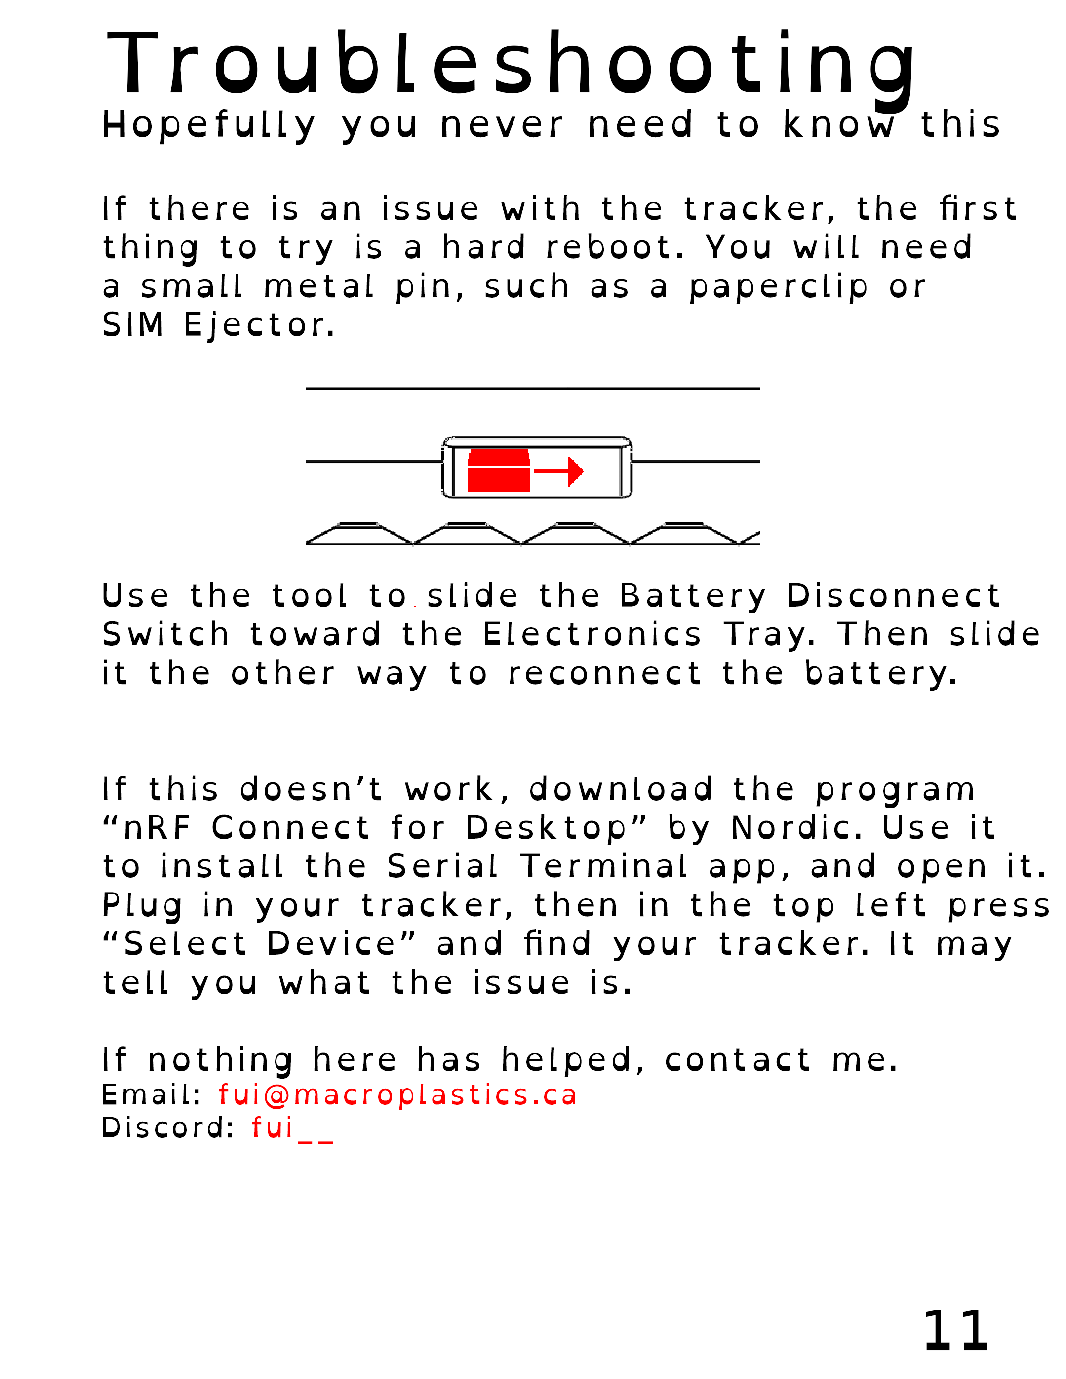
User manual/Individual pages/M.png
