Zipra1/SlimeNRF-Fuimini/User manual/Individual pages/N.png

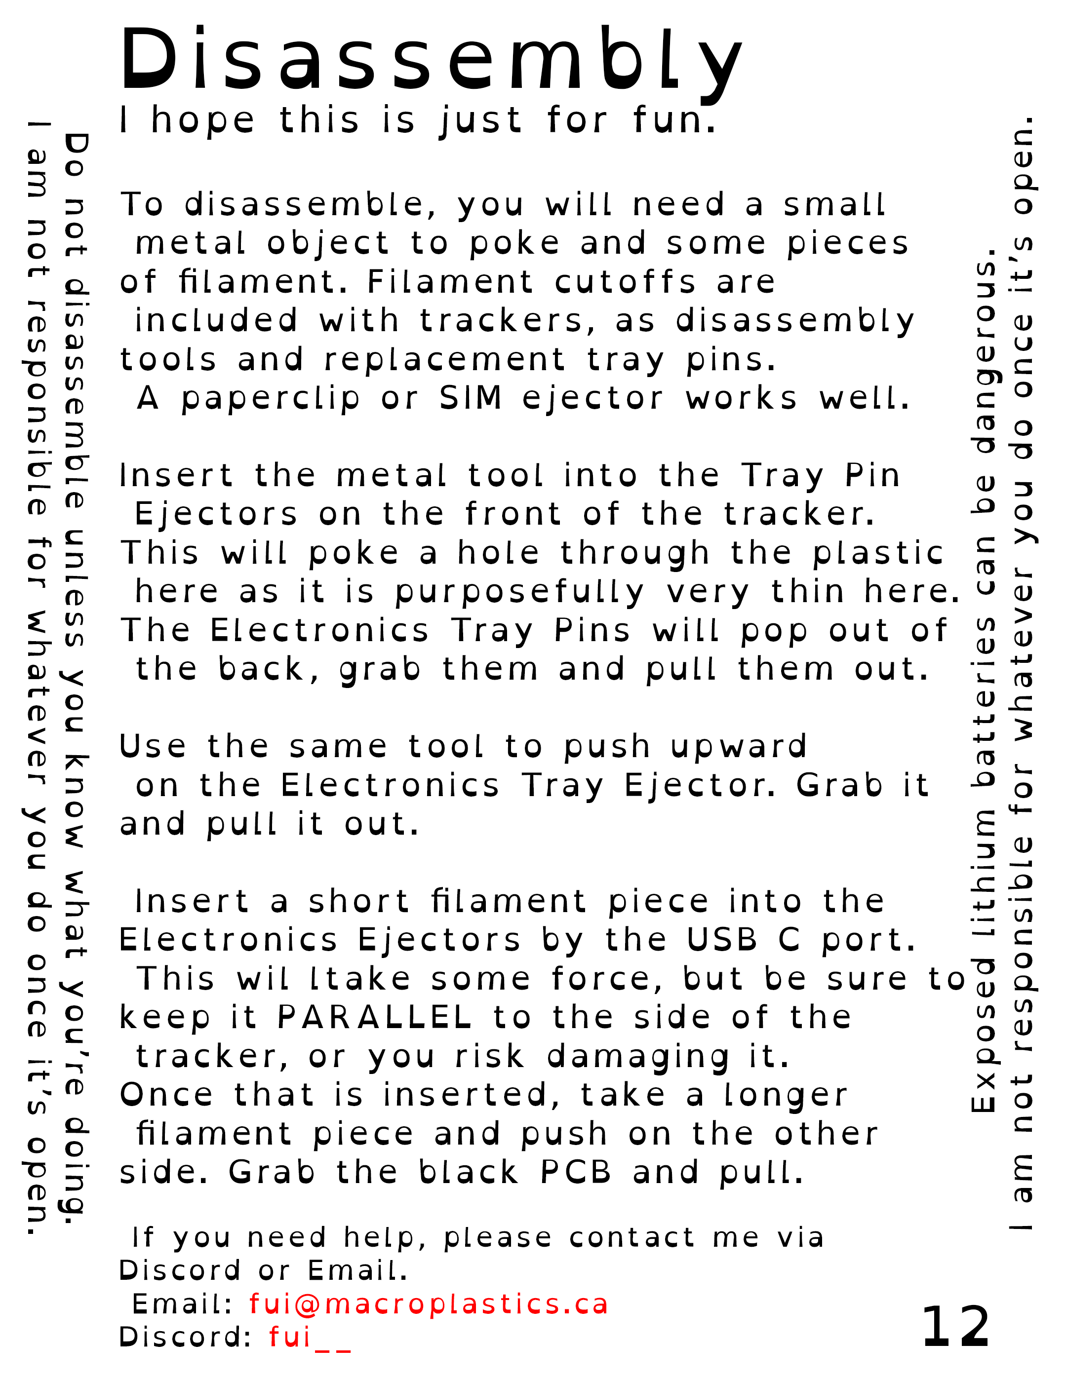
User manual/Individual pages/N.png
