Zipra1/SlimeNRF-Fuimini/User manual/Individual pages/O.png

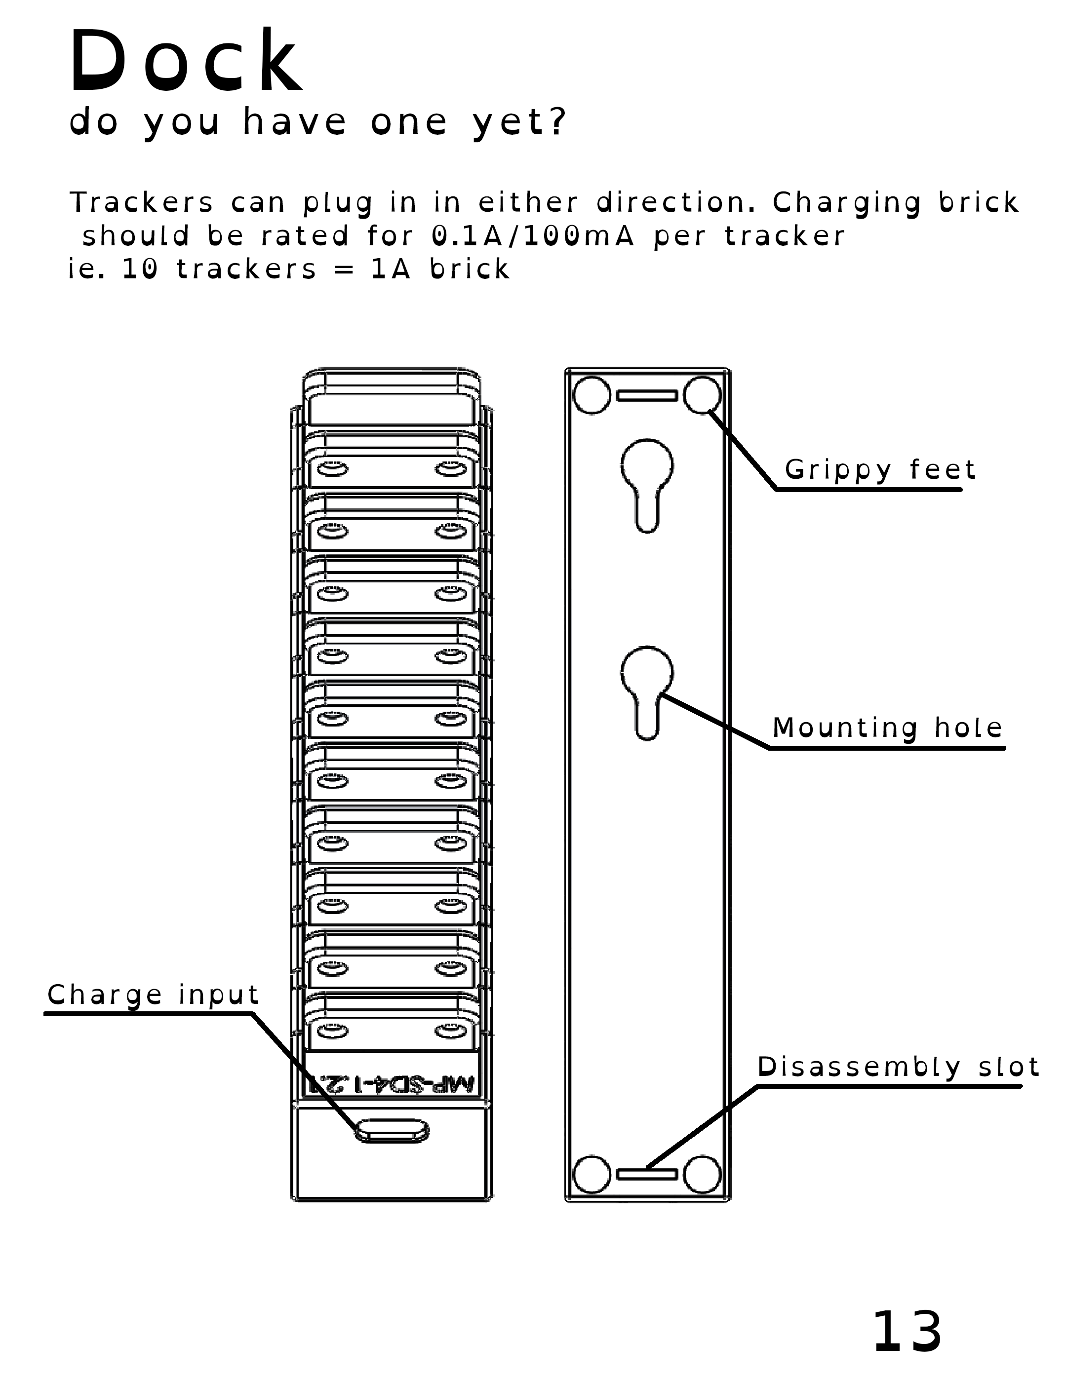
User manual/Individual pages/O.png
