Zipra1/SlimeNRF-Fuimini/User manual/Individual pages/P.png

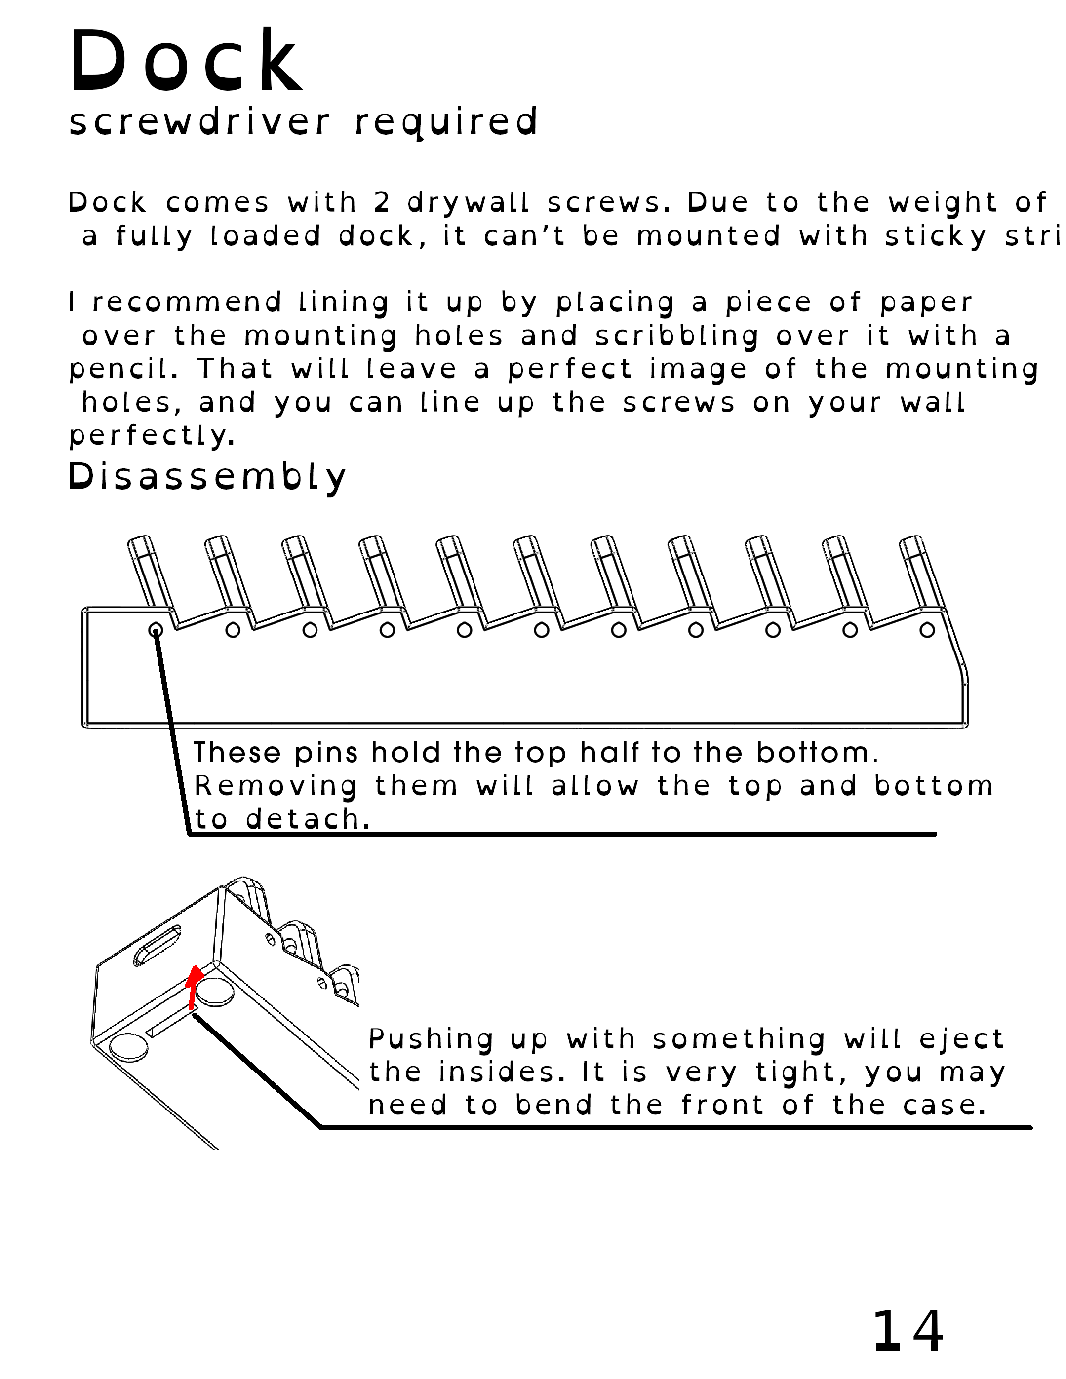
User manual/Individual pages/P.png
