Zipra1/SlimeNRF-Fuimini/User manual/Individual pages/Q.png

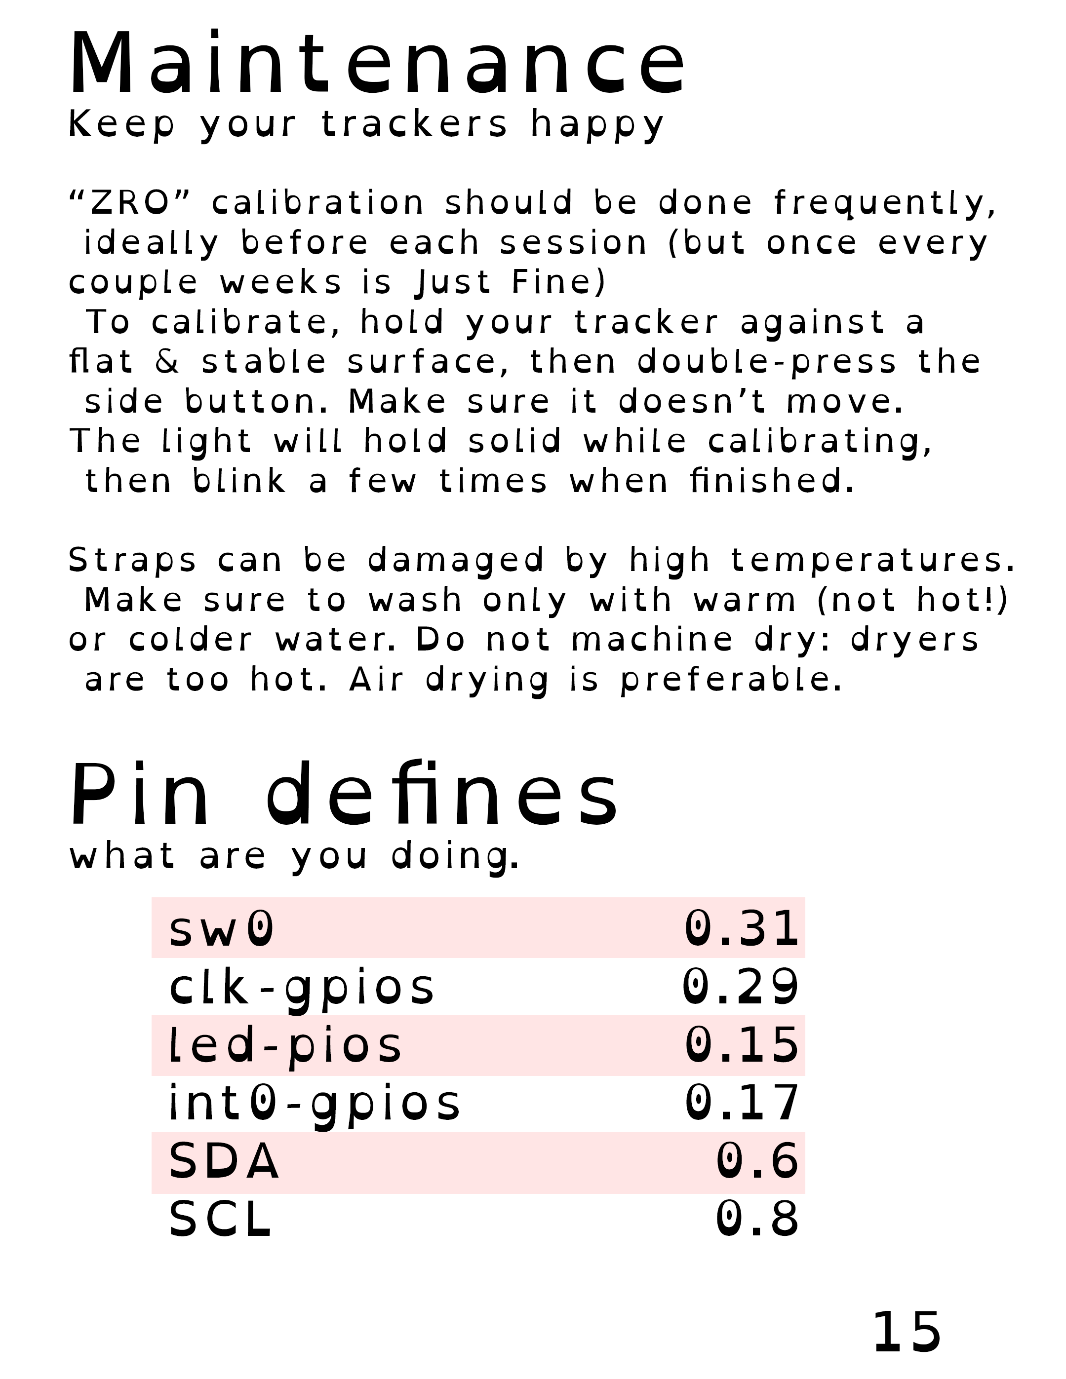
User manual/Individual pages/Q.png
