Zipra1/SlimeNRF-Fuimini/User manual/Individual pages/R.png

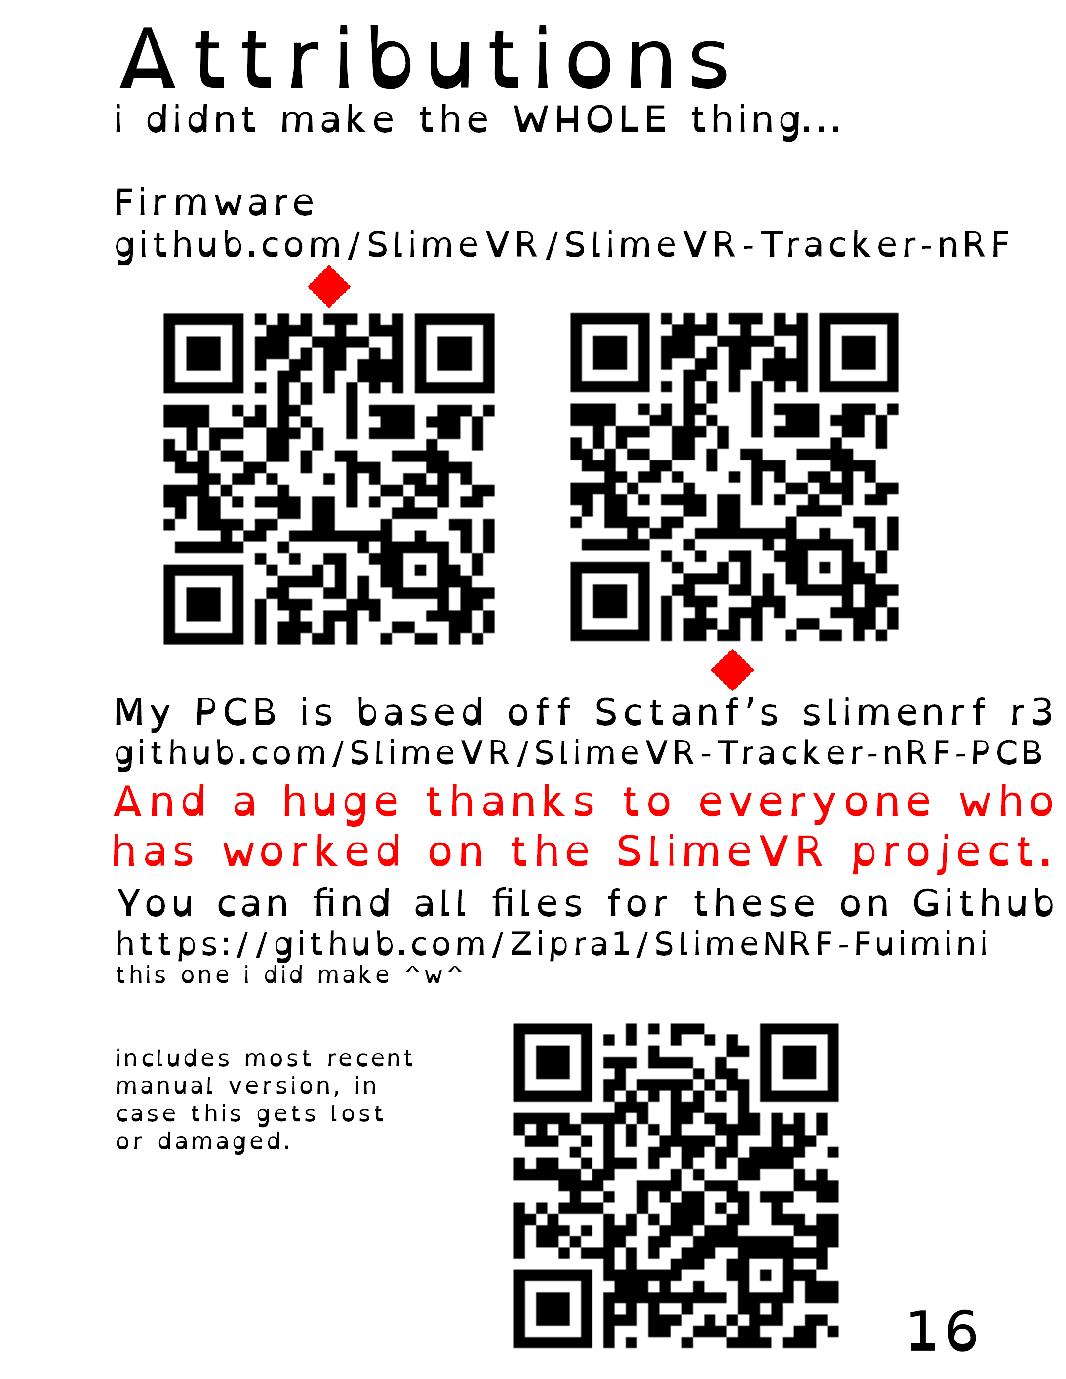
User manual/Individual pages/R.png
